Balner123/GPS_server_NodeJS/docs&LaTex/docs_server/0-packages.md

Below is a human-friendly summary of the main dependencies used by the project. For exact versions see `package.json`.

Dependencies:

- `bcryptjs` — password hashing
- `connect-flash` — flash messages for web UI
- `cors` — Cross-Origin Resource Sharing helper
- `dotenv` — load env vars from `.env`
- `ejs` — server-side view templates
- `express` — web framework
- `express-rate-limit` — rate limiting middleware
- `express-session` — session management
- `express-validator` — request validation
- `mysql2` — MySQL driver for Sequelize
- `nodemailer` — sending emails (verification, notifications)
- `passport` — authentication framework
- `passport-github2` — GitHub OAuth strategy
- `passport-google-oauth20` — Google OAuth strategy
- `sequelize` — ORM for MySQL
- `swagger-jsdoc` — JSDoc -> OpenAPI generation
- `swagger-ui-express` — serve Swagger UI

DevDependencies:

- `nodemon` — automatic server restart during development

Installation (from `package.json`):

- `npm install`
