Balner123/GPS_server_NodeJS/LilyGO-T-A76XX-main/MAIN/FINAL/docs_hw/4-data-format.md

# Formát dat a API

Tento dokument definuje přesnou podobu datových payloadů a chování komunikace mezi firmwarem a backendem. Preferujte krátké a stálé JSON payloady; rozsáhlejší ukázky uložte jako vzory v `docs_hw/schemas/`.

## Endpointy

- Upload dat: `POST http(s)://<server>[:<port>]/api/devices/input`
- Handshake: `POST http(s)://<server>[:<port>]/api/devices/handshake`
- Registrace (OTA): `POST http(s)://<server>[:<port>]/api/devices/register`

Poznámka: port 80 značí HTTP, jiný port než 443 znamená explicitně uvedené portování v URL; preferujte HTTPS.

## Struktura uploadu

Upload probíhá dávkově — jako pole JSON objektů. Každý objekt reprezentuje buď polohový záznam, nebo stavový záznam (např. potvrzení `power_status`).

Schematický příklad záznamu polohy (stručný):

```json
{
	"device": "<installationId>",
	"name": "<deviceName>",
	"latitude": <number>,
	"longitude": <number>,
	"speed": <number>,
	"altitude": <number>,
	"accuracy": <number>,
	"satellites": <number>,
	"power_status": "ON|OFF",
	"timestamp": "2025-01-01T12:00:00Z"
}
```

Stavový záznam (příklad):

```json
{
	"device": "<installationId>",
	"power_status": "OFF"
}
```

Poznámky k polím:
- `device` — identifikátor zařízení (posledních 10 hex znaků MAC bez dvojteček).
- `timestamp` — musí být ISO 8601 v UTC; interně se drží epoch milliseconds a serializuje se při odeslání.

## Dávkování a trvaní session

- `send_cached_data()` čte maximálně 15 záznamů na jeden upload (implementační limit `MAX_BATCH_SIZE`). Poznámka: server je navržen tak, aby bezpečně zpracoval až 15 položek; větší dávky mohou způsobit HTTP 500.
- Po úspěšném potvrzení jsou odeslané položky z cache odstraněny; neúspěšné položky zůstávají pro opakování.
- V průběhu jedné GPRS session probíhá nejprve handshake a následně upload dat.

## Formát odpovědi

Typická odpověď backendu (stručná):

```json
{
	"success": true,
	"registered": true,
	"config": {
		"interval_gps": 120,
		"interval_send": 5,
		"satellites": 4,
		"mode": "batch"
	}
}
```

- `success` — indikace přijetí dávky.
- `registered` — pokud `false`, zařízení přechází do bezpečného režimu.
- `config` — volitelné parametry, které zařízení aplikuje okamžitě.

HTTP stavové kódy a chování:
- 200: standardní odpověď s JSON → aplikovat konfiguraci.
- 403: vyžadovat odhlášení (FORCE_LOGOUT).
- 404/409: považovat za neregistrované zařízení → přepnout `registered=false`.
- ≥500 nebo síťová chyba: zachovat data v cache a opakovat později.

## Handshake

Handshake se provádí vždy před odesíláním dat v rámci GPRS session. Odesílaný payload (stručně):

```json
{
	"device_id": "<installationId>",
	"client_type": "HW",
	"power_status": "ON|OFF"
}
```

Odpověď může obsahovat pole `registered`, `config` a `power_instruction` (`TURN_OFF` / `NONE`). Hodnota `TURN_OFF` by měla vést k potvrzení a následnému řízenému vypnutí.

## Registrace (OTA)

Endpoint `/api/devices/register` přijímá registrační payload obsahující `client_type`, `username`, `password`, `device_id` a `name`. Registrace vyžaduje aktivní GPRS spojení; po úspěchu se doporučuje restart do běžného režimu.

## Chování při chybách

- Neparsovatelná odpověď: logovat chybu, zachovat data v cache.
- Kritické chyby (`404`, `409`): přepnout `registered=false` a čekat na servisní zásah.
- Síťové chyby a 5xx: zachovat data a opakovat během dalšího cyklu.
