Balner123/GPS_server_NodeJS/docs&LaTex/requirements_examples/lacheta_zaverecna-prace.md

Zde je kompletnì zpracovaný dokument do formátu **Markdown**. Zachoval jsem strukturu nadpisù, zvýraznìní kódu (C++) a formátování seznamù.

***

# ZÁVÌREÈNÁ STUDIJNÍ PRÁCE
## Dokumentace: Robotická ruka s využitím EMG

**Škola:** SŠPU Opava (Støední škola prùmyslová a umìlecká, Opava)  
**Autor:** Václav Lacheta  
**Obor:** 18-20-M/01 INFORMAÈNÍ TECHNOLOGIE se zamìøením na poèítaèové sítì a programování  
**Tøída:** IT4  
**Školní rok:** 2021/2022

---

### Podìkování
Dìkuji doc. Ing. Petru Èermákovi, Ph.D. za odborné konzultace a rady, které mi poskytl bìhem øešení mého projektu.

### Prohlášení
Prohlašuji, že jsem závìreènou práci vypracoval samostatnì a uvedl veškeré použité informaèní zdroje.

Souhlasím, aby tato studijní práce byla použita k výukovým úèelùm na Støední prùmyslové a umìlecké škole v Opavì, Praskova 399/8.

**V Opavì 31. 12. 2021**  
*(podpis autora práce)*

---

## ANOTACE

Souèástí práce bylo sestavení protetické ruky InMoov v životní velikosti ze souèástek vytisknutých na 3D tiskárnì. Umìlá ruka je ovládána pomocí elektromyografických (EMG) senzorù, díky nimž je možné získávat elektrické svalové signály a pøevádìt je na mechanické pohyby napodobující chování skuteèné lidské ruky. Ruka je upevnìna na podstavci obsahujícím nezbytný hardware vèetnì displeje a rotaèního enkodéru, který lze použít k ovládání. Zaøízení je možné ovládat manuálnì (natoèit každý prst do libovolného úhlu), pomocí EMG senzorù nebo zvolit nìkteré z naprogramovaných gest.

**Klíèová slova:** EMG, elektromyografie, InMoov, myoelektrická protéza, rotaèní enkodér, servomotor, Arduino, 3D tisk, displej

---

## OBSAH

1. **PROTÉZY**
    *   1.1 Historie protéz
    *   1.2 Klasifikace protéz
    *   1.3 Pasivní protézy
    *   1.4 Aktivní protézy
        *   1.4.1 Protézy pohánìné tìlem
        *   1.4.2 Myoelektrické protézy
        *   1.4.3 Hybridní protézy
2. **ELEKTROMYOGRAFIE**
    *   2.1 Svaly horní konèetiny
    *   2.2 EMG signály
    *   2.3 Snímání EMG signálù
3. **MOŽNÉ ZPÙSOBY ZPRACOVÁNÍ EMG SIGNÁLU A JEJICH IMPLEMENTACE V PROTÉZÁCH**
    *   3.1 Mikrokontrolery
    *   3.2 Senzory
    *   3.3 Pøíklady protéz
        *   3.3.1 Inteligentní humanoidní robotická ruka Sain
        *   3.3.2 Protetická ruka InMoov
4. **SESTROJENÍ RUKY**
    *   4.1 InMoov ruka
    *   4.2 Ovládaní servo motorù
    *   4.3 Ovládaní ruky pomocí EMG
    *   4.4 Displej a uživatelské ovládaní
    *   4.5 Podstavec
    *   4.6 Využité souèástky
*   **ZÁVÌR**
*   **SEZNAM POUŽITÝCH INFORMAÈNÍCH ZDROJÙ**
*   **SEZNAM PØÍLOH**

---

## ÚVOD

Nad výbìrem závìreèné práce jsem pøemýšlel dlouhou dobu. Hledal jsem takový projekt, pøi jehož øešení bych mohl uplatnit své znalosti programování mikrokontrolerù a využít i rozmanitou zásobu elektronických souèástek, které jsem nashromáždil v prùbìhu svého studia na støední škole. Zároveò jsem si pøál pustit se také do nìèeho nového, co by pøedstavovalo zajímavou výzvu pro mì samotného a pøípadnì bylo pøínosné i pro druhé.

Jednoho dne jsem zhlédl video s ukázkou robotické ruky, která se ovládá pomocí EMG senzorù. V tu chvíli jsem se rozhodl, že právì to bude téma mého závìreèného projektu. Navíc jsem vždy tento typ protézy považoval za nìco, co si nemùže normální smrtelník sestavit doma, takže jsem byl i hodnì zvìdavý, zda se mi to povede.

Nyní tedy pøedkládám výsledek své práce, která trvala nìkolik mìsícù. Podaøilo se mi dosáhnout vìtšiny dílèích cílù, které jsem si vytyèil. Z finanèních dùvodù jsem si bohužel nemohl dovolit poøídit více EMG senzorù a musel jsem si vystaèit pouze s jedním, pomocí kterého dokáži monitorovat sevøení nebo otevøení pìsti a následnì tento pohyb pøevést na robotickou ruku.

V praxi se s mým øešením moc nesetkáme, tento zpùsob se spíše využívá ve svìtì medicíny a bioinformatiky pro diagnostiku. Vyspìlejší protézy se spíše zamìøují na umístìní elektrod uvnitø svalu, jelikož jsou získávány mnohem pøesnìjší signály.

V úvodní kapitole své dokumentace se zabývám vývojem protéz v historii a popisuji nìkterá zajímavá technická øešení, která se objevila v minulosti i ta, která se používají dnes. Další èást je zamìøena na problematiku elektromyografie, jež studuje strukturu kosterní svaloviny a elektrické biosignály, které ze svalù vycházejí. Díky poznatkùm tohoto oboru mùžeme využívat EMG senzory a snímat pomocí nich impulzy lidského tìla. Nejdùležitìjší èást mé práce je podrobnìji vìnována technickému a programovému øešení projektu InMoov ruky.

---

# 1. PROTÉZY

Protézu lze definovat jako „umìlé zaøízení, které nahrazuje nebo doplòuje chybìjící èi narušenou èást lidského tìla“.

V dnešní dobì existuje mnoho rùzných typù protéz. Ty se pohybují od kosmetických ozdob pøes jednoduché pasivní mechanické pomùcky, jako jsou rùzné háky a podobnì, až po elektricky pohánìné protézy, které mohou alespoò èásteènì obnovit funkci chybìjící konèetiny.

## 1.1 Historie protéz
Myšlenka umìlého nahrazení ztracených konèetin existuje již tisíce let. Existují protézy, které jsou více než 3000 let staré. Pøíkladem je takzvaný „káhirský prst“, který byl nalezen u egyptské mumie a mìl nahradit ztracený palec u nohy. Protézy, jako je tato, byly kdysi vyrábìny pomocí pøírodních surovin: kùže, døeva èi lnu.

*Obrázek 1: Káhirský prst*

V roce 300 pøed naším letopoètem byla Øímany vyrobena první známá protetická noha, takzvaná „noha Capua“. Byla vyrobena ze železa a bronzu a mìla døevìné jádro. Bìhem této doby se objevily protézy, jako jsou ruèní háky a kolíkové nohy, které umožòovaly chùzi nebo držení štítù. Ty byly sestrojeny pøevážnì ze železa a oceli.

V dobì renesance udìlala anestezie a léèba ran veliký pokrok, amputace proto byly bezpeènìjší než kdy døíve. S novými možnostmi amputace se zaèaly šíøit vynálezy, jakým byl napøíklad tzv. turniket, které pomohly zastavit tìžké krvácení v prùbìhu amputace. Vznikaly nové typy protéz - napøíklad „železná ruka rytíøe Götz von Berlichingen“, s níž bylo možné pohybovat a manipulovat pomocí pružinového mechanismu uvnitø ruky. V této dobì se na protézy používalo pøedevším železo, ocel, mìï a døevo.

V období americké obèanské války, ale i bìhem svìtových válek zažila protetika velký posun vpøed vyplývající z vysokého poètu zmrzaèených vojákù. Kromì toho byl vyvinut i zcela nový materiál - pryž, který doplòoval døívìjší protézy ze døeva a kùže.

V letech po druhé svìtové válce bylo objeveno mnoho dalších materiálù, díky kterým se døevo a kùže staly nepotøebnými. Patøí mezi nì pryskyøice, polykarbonát, plast a lamináty. Díky jejich použití se protézy staly lehèí a odolnìjší.

Materiálové složení se v posledních letech dále zdokonaluje a v souèasnosti vznikají vysoce výkonné protézy, které mají vyšší stabilitu, pohodlí a nižší hmotnost. Kromì toho mohou být souèástí protéz senzory umožòující aktivní ovládaní pomocí mikroprocesorù. Vývoj moderních protéz se mùže opøít i o nové výrobní procesy, jako je 3D tisk, který umožòuje vyrobit velmi jednoduché i levné protézy.

*Obrázek 1.2: Noha Capua | Obrázek 1.3: Ruka Götz von Berlichingen*

## 1.2 Klasifikace protéz
Protézy mùžeme rozdìlit na:

1.  **Pasivní.** Protézy, které nemají žádné pohyblivé èásti. Ty se vìtšinou používají pro estetické úèely. Existují také protézy urèené pro speciální úkoly, jako je zahradnièení nebo sport.
2.  **Aktivní.** Ty jsou naopak urèeny k podpoøe vyšší produktivity a funkènosti. Mají pohyblivé èásti, které jsou pohánìny buï samotným tìlem, nebo vnìjší energií. Navíc existují ještì hybridní kombinace, které jsou pohánìny èásteènì tìlem a èásteènì akèními èleny.

*Obrázek 1.4: Rozdìlení protéz*

Protézy mohou plnit dva rùzné úkoly, které se mohou zásadnì lišit. Na jednu stranu, protézy mají obnovit funkce, které byly ztraceny ztrátou konèetiny a na druhou stranu se protézy používají k optické obnovì „normálního stavu“ tìla. Protézy, které vizuálnì pøipomínají chybìjící konèetinu, mají èasto omezenou funkènost, zatímco funkèní protézy nejsou moc dobré po vizuální stránce. Proto existuje mnoho pacientù, kteøí mají nìkolik rùzných protéz, napøíklad jednu, která vizuálnì pøipomíná chybìjící konèetinu, a druhou, která je maximálnì funkèní.

## 1.3 Pasivní protézy
Kosmetické použití protéz je velmi dùležité, protože zejména horní konèetiny jsou èasto používané v sociálních interakcích, jako jsou gesta nebo bìhem komunikace. Vizuálnì nenápadný vzhled tak mùže pomoci vyhnout se psychickému stresu z dùvodu odlišnosti od ostatních. To platí zejména v pøípadì, kdy amputací není postiženo pouze pøedloktí, ale i paže. Nejlepší reprezentace pøirozené ruky poskytují pasivní kosmetické protézy. Lze je pøizpùsobit pacientovi pomocí tvaru a barvy; napøíklad napodobit barvu kùže a anatomické rysy, jako jsou znaménka, nebo dokonce ochlupení na pažích. Estetické protézy lze také použít pro jednoduché manuální úkoly, jako je fixace papíru pøi psaní. Obecnì jsou velmi lehké a mají vysoký komfort nošení.

*Obrázek 1.5: Pøíklad pasivní protézy*

## 1.4 Aktivní protézy
Nejèastìji se vyskytují protézy aktivní. Tyto mají pohyblivé èástí, které jsou pohánìny buï tìlem, nebo vlastním zdrojem energie. S tìlesnì pohánìnými protézami se ovládání provádí pohybem svalu v blízkosti amputované konèetiny. U myoelektrických protéz jsou akèní potenciály svalu monitorovány senzory a použity pro pohyb protézy. Aktivní protézy mohou mít mnoho podob, jako napøíklad ruce, pohyblivé háky nebo speciální tvary pro konkrétní pacienty. Tento druh protéz je obvykle tìžší než pasivní, jelikož jsou pro nì urèeny vìtší zátìže. Díky tomu jsou èasto vyrobeny z tìžších, ale odolnìjších materiálù, jako jsou kov nebo tvrzený plast. Úkolem aktivních protéz je obnovit funkènost postižených konèetin, a zejména ruka má velký význam pro manipulaci s objekty. Pomocí takových protéz je možné uchopovat pøedmìty a zvládat èinnosti v každodenním životì.

### 1.4.1 Protézy pohánìné tìlem
Protézy pohánìné tìlem jsou èasto oznaèovány jako „ovládané kabelem“, protože vyžadují ocelové kabely bìhem provozu. Obvykle jsou tyto postroje konstruovány tak, že popruh prochází pøes lopatku a pøipojuje se k tažnému lanku, které ovládá protézu. Protože protézy pohánìné tìlem jsou pøímo spojeny napøíklad s pohybem ramena, mají tak vysokou úroveò zpìtné vazby na základì napìtí na ovládacím kabelu. Dalšími výhodami tìchto protéz je, že jsou ve vìtšinì pøípadù vodotìsné a snadno se èistí. Jejich jednoduchý design umožnuje postiženým osobám se je rychleji nauèit ovládat, a navíc stojí výraznì ménì ve srovnání s aktivnì øízenými.

Nevýhodou tìchto protéz je, že k ovládání potøebují postroj k ovládání. To znamená, že postižené osoby musí mít urèitou sílu a svobodu pohybu, aby mohly takové zaøízení ovládat. Navíc jsou tyto protézy èasto vizuálnì ménì pøitažlivé ve srovnání s elektricky pohánìné, a to kvùli postroji.

Protézy s takovým mechanickým pøenosem síly jsou oblíbenìjší než ty elektrické. Devadesát procent lidí, kteøí mají aktivní protézu, používají protézu pohánìnou tìlem. Jejich nejvìtšími klady jsou nízká hmotnost, odolná konstrukce a lepší haptická odezva generovaná kabely.

*Obrázek 1.6: Pøíklad protézy pohánìné tìlem*

### 1.4.2 Myoelektrické protézy
Tyto protézy jsou pøevážnì elektrické. Mají externí zásobník energie, který napájí vestavìné akèní èleny. Obecnì se energie ukládá ve formì akumulátoru. Tato zaøízení lze ovládat více vstupy, jako jsou elektromyografické (EMG) signály, zpìtná vazba motorù a také vyhrazené spínaèe. Takové fyzické spínaèe jsou zvláštì užiteèné u vážných amputací. Je to proto, že v takových pøípadech obvykle existuje mnoho rùzných motorù, jsou zapotøebí rùzné spoje a je tøeba je ovládat samostatnì.

Nicménì myoelektrické protézy se ještì èastìji používají u ménì vážných amputací. Myoelektrické protézy jsou založeny na mìøení elektrického vzruchu ve svalech. Elektrody pøipojené ke svalùm mìøí elektrické signály z kontrakcí kosterního svalstva. Zmìny elektromagnetických polí, které vznikají pøi napnutí svalu, zachycuje povrch elektrody a jsou v podobì napì�ových signálù posílány do mikrokontroleru.

Ve vìtšinì pøípadù jsou elektrody pøipevnìny ke dvìma svalùm, které vykonávají pohyb v urèitém smìru, jako je extenzor zápìstí a flexor zápìstí. Pro tento úèel se používá jeden sval pro jeden smìr pohybu protézy. Napøíklad napnutím jednoho svalu se otevøe dlaò a napnutí protikusu se dlaò uzavøe. Aby se zabránilo nedobrovolným pohybùm, jsou pro signály EMG nastaveny prahové hodnoty. Teprve po pøekroèení urèitého prahu se protéza zaène pohybovat.

Jednou z výhod takové myoelektrické protézy je, že umožòuje vìtší uchopovací síly ve srovnání s protézami pohánìnými tìlem. V nìkterých pøípadech to mùže být výhodné pøi držení objektù na delší dobu. Kromì toho nejsou pro úèely ovládání potøeba žádné postroje. To dovoluje ovládání více os a kloubù souèasnì. Absence postroje také umožòuje, aby vypadaly více jako skuteèné konèetiny.

Existují však také dùvody, proè jsou protézy pohánìné tìlem 10krát populárnìjší než myoelektrické. Je to dáno pøedevším vyšší poøizovací cenou takových zaøízení. Navíc jsou ménì robustní a kvùli vestavìné elektronice jen èásteènì vodotìsné. Protože mezi nimi není žádné mechanické spojení zbývající konèetiny s protézou, je haptická zpìtná vazba horší. Nìkdy je pro postižené tìžší, aby správnì vyhodnotili a použili požadovanou uchopovací sílu. Kromì toho se tyto protézy kvùli složité konstrukci snadnìji lámou a musí být èastìji servisovány.

Elektrody jsou jejich další nevýhodou, nebo� se mùže stát, že se pohnou nebo ztratí kontakt. V tìchto pøípadech nelze protézy správnì provozovat. Konstantní kontakt s elektrodami mùže také zpùsobit podráždìní kùže nebo nepøíjemný pocit, pokud protéza není správnì upravená. Pøesto se tyto protézy neustále vyvíjejí a mohly by být v budoucnu více rozšíøené.

*Obrázek 1.7: Myoelektrická protéza*

### 1.4.3 Hybridní protézy
Existují i protézy, které se skládají z kombinace tìlesnì pohánìných a myoelektrických. Tato kombinace umožòuje využít výhody obou typù, napøíklad mohou dosáhnout vysokých uchopovacích sil pøi zachování nízké hmotnosti protézy. Navíc tento pøístup mùže usnadnit ovládání protézy.

---

# 2. ELEKTROMYOGRAFIE

## 2.1 Svaly horní konèetiny
Kosterní svaly jsou souèástí svalstva odpovìdné za aktivní pohyby tìla, a tedy i souèástí jednoho ze tøí hlavních typù svalù. Stejnì jako srdeèní svaly patøí kosterní svaly do skupiny pøíènì pruhovaných svalù a oznaèují se také jako dobrovolné svaly. Až na pár výjimek, jsou tyto svaly napojeny na kost šlachami. Èasto existují v párech, pøièemž první sval je primárním hybatelem a druhý je jeho antagonistou. Napøíklad, biceps a triceps jsou taková dvojice antagonistù. Když se jeden z nich stáhne, druhý se uvolní a umožní pohyb a naopak.

Kosterní svaly mají složitou strukturu. Skládají se z fasciklù, které jsou svazky prodloužených svalových vláken. Samotná svalová vlákna se skládají ze svazkù myofibril. Samotné myofibrily jsou tvoøeny z myozinových a aktinových vláken. Tato dvì vlákna jsou naskládaná v pravidelnì se opakujících sestavách a jsou zodpovìdná za samotnou kontrakci svalù klouzáním proti sobì navzájem. Tato myozinová pole se nazývají sarkomery. Motorické neurony, které øídí kontrakci, jsou spojeny ve snopci svalových vláken a spoleènì se nazývají motorická jednotka.

**Nejdùležitìjší svaly jsou:**
1.  *Musculus pectoralis major* (velký sval prsní)
2.  *Musculus deltoideus* (deltový sval)
3.  *Musculus bizeps brachii* (dvojhlavý sval pažní)
4.  *Musculus trizeps brachii* (trojhlavý sval pažní)
5.  *Musculus brachioradialis* (sval vøetenní)
6.  *Musculus flexor digiti* (sval který zajištuje ohýbaní prstù)

*Obrázek 2.1: Svaly horní konèetiny*

Motorické neurony se nacházejí uvnitø mozkového kmene a míchy a jsou spojeny se svalem pøes axony, který mohou pøenášet excitaèní signál na velké vzdálenosti. Aktivace svalových vláken se dìje elektrickými potenciály bunìèných membrán. Díky otevíráním a zavíráním iontových kanálù umožòují membrány pohyb iontù a vytvoøit tak signál elektromagnetického pole. Tento signál cestuje podél axonù jako vlna a skonèí v motorickém neuronu. Místo, kde se motorické neurony spojují se svalovými vlákny, se nazývá neuromuskulární spojení. To je místo, kde vlákna zaènou reagovat na signál motorického neuronu a tím zaènou kontrakce.

*Obrázek 2.2: Struktura kosterního svalu*

## 2.2 EMG signály
Akèní potenciály se vytváøejí bìhem kontrakce kosterní svaloviny. Tyto akèní potenciály se dají mìøit a jsou také základem EMG signálù. EMG signály jsou používané pro analýzu a klinickou diagnostiku v biomedicínských aplikacích, jako jsou rehabilitace pohybových vad. Elektrické proudy generované bìhem procesu flexe lze mìøit pomocí elektrod na svalu nebo uvnitø svalu. EMG signály jsou pomìrnì komplikované, protože jsou závislé na anatomii fyziologické vlastnosti svalu. Neèistoty tìchto signálù jsou zcela bìžné a hromadí se pøi cestování tìlem. Signál EMG je také sumou nìkolika motorických jednotek, které vysílají ve stejnou dobu, a tak mùže docházet k interakcím mezi tìmito rùznými signály.

Intervaly, ve kterých se vyskytují akèní potenciály konkrétní motorické jednotky, jsou náhodné. Samotný akèní potenciál motorické jednotky je kombinací akèních potenciálù svalových vláken patøící k jedné motorické jednotce. Lze to popsat vzorcem níže:

$$x(n) = \sum_{r=0}^{N-1} h(r)e(n-r) + w(n)$$

V tomto vzorci je:
*   `x(n)` výsledný EMG signál,
*   `e(n)` impuls odpalu n,
*   `h(r)` akèní potenciál motorické jednotky,
*   `w(n)` aditivní bílý Gaussùv šum,
*   `N` poèet støel motorických jednotek.

*Obrázek 2.3: Dekompozice EMG signálu*

## 2.3 Snímání EMG signálù
EMG signály jsou snímány elektrodami, které jsou buï umístìny na kùži nad svalem, nebo uvnitø svalu. Obì varianty mají svá pro a proti. Pøi použití intramuskulárních senzorù musí být prostøedí a senzory sterilizovány, protože se jedná o invazivní postup, který nese velké riziko pøenosu nemoci nebo spuštìní infekce. Na druhou stranu, jakmile je elektroda umístìna, tak nezpùsobuje žádné nepohodlí a signály nejsou zkresleny tkánìmi svalù a kùže. Tento proces vede k vìtší èistosti signálu nad šumem.

Na druhou stranu, povrchové elektrody mohou být kdykoliv pøemístìny, pokud poloha není vhodná a nepotøebuje k tomu žádné invazivní postupy. Vìtšinou se povrchové elektrody využívají pro krátká mìøení. Je velmi dùležité elektrody správnì umístit a používat elektrody pro konkrétní úkol, výbìr místa totiž velice ovlivní získaný signál. Chceme-li získat nejvyšší sílu signálu, tak elektrody musí být umístìny uprostøed svalu ve smìru svalových vláken. Nejèastìjší používané elektrody jsou Ag/AgCL, protože nejsou polarizovatelné a umožnují proudový tok kùže. Ve vìtšinì pøípadù jsou pøipevnìny pomocí vodivého gelu pro snížení impedanci kùže.

Obvykle se používají `2n + 1` elektrody. Dvì pro každý kanál `n` a jedna referenèní (uzemòovací) elektroda, která je umístìna na elektricky nesouvisející tkání.

Poté, co je signál zachycen, je obvykle zesílen, protože jeho amplituda je pomìrnì malá. Pro první etapu zesílení se bìžnì používá diferenciální zesilovaè. Diferenciální zesilovaè se používá k eliminaci spoleèných proudù. Signál je snímán na tøech místech, dvì detekèní elektrody a jedna referenèní, která definuje neutrální zem, kterou sdílejí další dvì elektrody. Jakýkoliv spoleèný signál pro tyto dvì elektrody bude odstranìn, naopak signály, které nesdílejí, budou poté zesíleny.

Poté se použije zesilovaè k dalšímu zvýšení amplitudy signálu. Pro eliminaci vysokého šumu se používá pláš� nízko propustného filtru frekvence. Dále lze použít usmìrnìní signálu pro pøeklopení èástí negativního signálu na pozitivní. Nakonec je použit A/D pøevodník, aby poèítaè nebo mikrokontroler mohl pracovat se signálem EMG.

*Obrázek 2.4: Schéma nahrávaní EMG*

---

# 3. MOŽNÉ ZPÙSOBY ZPRACOVÁNÍ EMG SIGNÁLU A JEJICH IMPLEMENTACE V PROTÉZÁCH

## 3.1 Mikrokontrolery
Je na výbìr nìkolik možností. První možností je použít mikrokontroler k mìøení svalové aktivity a vyhodnocování signálu. Napøíklad Arduino Uno je založeno na èipu ATMEL ATmega328, pracuje na frekvenci 16 MHz a mùže komunikovat s ostatními zaøízeními pøes UART, SPI a I2C. Kromì toho vstupní a výstupní (GPIO) piny lze použít k ovládání rùzných dalších periferií nebo ke ètení analogových a digitálních signálù díky vestavìnému 10bitovému A/D pøevodníku. Další výhodou tìchto vývojových desek je, že je lze jednoduše programovat a nevyžadují vyhrazené pøístupy a bitové manipulace jednotlivých registrù, navíc jsou takové desky dost rozšíøené, snadno dostupné a existuje velké množství už vytvoøených kódù a dokumentací pro další usnadnìní programování.

Nevýhodou však bývá výkon použitých procesorù, protože musí být co nejmenší a energeticky efektivní, mají èasto jen omezený výkon. To znamená, že na tìchto zaøízeních lze provádìt pouze jednoduché matematické operace, a to mùže mít významný dopad na výkon celého systému, zejména pro aplikace v reálném èase, jako je EMG analýza. Kvùli nízkému výkonu nemusí být signály naèteny vèas a zpracování mùže trvat déle, což má za následek velké zpoždìní v celém systému nebo omezenou funkènost, proto je lepší se dívat po dalších výkonnìjších mikrokontrolerech.

## 3.2 Senzory
Prvním krokem pøi získávání dat je identifikace správných pozic pro elektrody. Aby bylo možné správnì rozeznávat pohyby jednotlivých prstù, je potøeba použít nìkolik svalových signálù. Na monitorování každého prstu je potøeba minimálnì 4 senzory èili 4 kanály. Jeden pro palec, jeden pro prostøedníèek, jeden pro ukazováèek a jeden senzor pro prsteníèek a malíèek dohromady. Nejlépe je použít 5 senzorù, aby mìl každý prst vyhrazený kanál.

Celkem máme tedy 11 elektrod. Pìt párù po dvou elektrodách a další referenèní elektrodu. Tato referenèní elektroda je umístìna na zadní stranì pøedloktí v úrovni loktu, protože tam se dá oèekávat malá svalová aktivita, nebo na kosterní èásti ruky. Senzory jsou poté pøipojeny k samotným elektrodám, aby zesílily a pøenesly signál do mikrokontroleru.

V dnešní dobì jsou EMG senzory pomìrnì dost rozšíøené a máme na výbìr hned nìkolik rùzných senzorù od rùzných firem. Ve své práci jsem použil senzory **MyoWare od Advancer Technologies**. Tyto senzory lze provozovat pro napìtí 3,3 V nebo 5 V. Logika zpracování svalového signálu je øešena pøímo na senzorech, tudíž z nich mùžeme èíst obálku signálu. Pokud je pro tuto funkci nechceme použit, mùžeme zachytit i surový EMG signál a zpracování si øešit potom sami. Zesílení signálu lze nastavit pomocí potenciometru. Výstupní analogový signál už potom èteme a zpracováváme na mikrokontroleru.

*Obrázek 3.1: Myoware muscle sensor*

## 3.3 Pøíklady protéz

### 3.3.1 Inteligentní humanoidní robotická ruka Sain
Tato robotická ruka se dá velmi snadno používat, protože už je pøedem složená.

*Obrázek 3.2: Sain Smart 5-DOF*

### 3.3.2 Protetická ruka InMoov
Protetická ruka InMoov nabízí lepší zpùsob zobrazení pohybù. Je souèástí projektu s otevøeným zdrojovým kódem, který založil francouzský sochaø a designér Gael Langevin. Projekt InMoov se skládá ze stovek 3D tisknutých dílù, které lze pøipojit k pohonùm a vytvoøit tak robota v životní velikosti. Jednotlivé konèetiny lze ovládat a rozpohybovat pomocí motorù. Stejnì jako u ruky Sain Smart lze prsty ovládat jednotlivì. To se také provádí pomocí 5 serv, které se montují do pøedloktí a ovládají prst pøes provázky. Jedno servo mùže být použito k otáèení ruky kolem zápìstí. Ve srovnání s rukou Sain Smart používají InMoov vìtší a mnohem silnìjší serva. Kromì toho návrh prošel nìkolika designovými iteracemi a neustále se pøizpùsobuje a zlepšuje.

*Obrázek 3.3: Robot InMoov*

---

# 4. SESTROJENÍ RUKY

Kompletní sestrojení ruky se rozdìlovalo na více èástí.
*   Sestrojení mechanické èasti ruky.
*   Ovládaní servo pohonù na ruce.
*   Ovládání pomocí EMG senzorù.
*   Ovládaní pøes uživatelské rozhraní.
*   Sestrojení podstavce pro zlepšení vzhledu a manipulace.

## 4.1 InMoov ruka
Pro svùj projekt jsem zvolil sestrojení protetické ruky InMoov. Na InMoov webu jsou dostupné všechny díly a také podrobný návod jak ruku složit. Celá ruka se skládá z 50 rùzných dílù. Díly jsou vytisknuté z PETG materiálu. Vìtšinou se díly lepily k sobì, ale nìkteré jsou i našroubované.

Ve spodní èásti ruky je pøimontovaných pìt MG995 servo pohonù, které pohybují s prsty. Další MG995 servo je pøimontované v zápìstí pro otáèení dlanì.

Èlánky prstù jsou k sobì lepené a pro klouby je využita válcovitá tyè o prùmìru 3 mm, která slouží jako èep. Èlánky prstu jsou pøes pomocné vodicí díry propleteny vždy dva stejnì dlouhé rybáøské pletence. Na koneècích prstù jsou dva provázky svázané k sobì, aby utvoøily jeden.

Dále jsou provázky propletené pøes dlaò až po zápìstí a tam jsou navázané na serva, které je napínají a tím napodobují funkci šlachy: když servo zatáhne za jeden konec provázku, prst se ohne a když zatáhne za druhý, tak se prst znova otevøe.

*Obrázek 4.1: Díly k ruce | Obrázek 4.2: Spodní èást ruky | Obrázek 4.3: Servo na otáèení dlanì | Obrázek 4.4: Dlaò | Obrázek 4.5: Koneèky prstù | Obrázek 4.6: Propletení provázku pøes ruku*

Provázky jsou namotané na kroužky servo motorù a pomoci dvou šroubkù se provázek napne. Všechna serva ovládá Micro Maestro 6-Channel od Pololu, který komunikuje s Arduinem pøes protokol UART.

*Obrázek 4.7: Sestavená ruka*

## 4.2 Ovládaní servo motorù
Micro Maestro, které ovládá servo pohony a Arduino spolu komunikují pomocí protokolu UART èili pøes RX a TX piny na desce. Protože Arduino UNO má dva vyhrazené RX a TX piny, které jsou potøeba pro nahrávání kódu, tak si je simuluji na jiných pinech pomocí knihovny `SoftwareSerial.h`.

Díky knihovnì pro Micro Maestro už šlo samotné programování pohybu serv jednoduše. Pro zefektivnìní a pro lepší pøehlednost kódu jsem vytvoøil tøidu `Arm`, která obsahuje veškeré potøebné metody k ovládaní serv, jako jsou `openIndex()`, `closeIndex()`, `getIndexPos()` a další.

```cpp
void Arm::openPinky()const{
    maestro.setTarget(this->pinky,this->open);
    return;
}

void Arm::closeThumb()const{
    maestro.setTarget(this->thumb, close);
    return;
}
```

## 4.3 Ovládaní ruky pomocí EMG
Mým cílem bylo monitorovat každý prst, ale v prùbìhu jsem zjistil, že tento cíl je dosti vzdálený z dùvodu nedostatku financí. Cena tìchto senzorù je pomìrnì dost vysoká.

Rozhodl jsem se proto pro jednodušší øešení pouze s jedním senzorem a monitorování otevøení a sevøení pìsti. Èást kódu, která se stará o ovládání ruky pomoci EMG senzorù, je pomìrnì dost jednoduchá. Když si necháme vypisovat hodnoty ze senzorù na graf, tak dostaneme takovýto výsledek.

Z grafu jde vidìt, že když zatneme pìst, tak hodnota rapidnì vzroste, protože v tu chvíli projde pøes senzor elektrický proud. Poté jsou hodnoty zase nízké, i když držíme zatnutou pìst. Hodnota opìt vzroste, když pìst uvolníme.

Èili když hodnota bude vìtší než naše nastavená prahová hodnota, tak se pohne servy tak, aby utvoøily pìst.

*Obrázek 4.8: Graf EMG hodnot | Obrázek 4.9: Graf EMG hodnot (detail)*

Problémem je, že nevíme, kdy má uživatel sevøenou pìst a kdy ne, protože nárùsty hodnot jsou témìø stejné v obou pøípadech. Èili pro moje øešení jsem použil jednoduchý pøepínaè, který pøepíná mezi stavy pìst a dlaò. Nárùst hodnoty trvá nìjakou chvílí, takže ještì pøed pøepnutím stavu se poèká 250 ms, než k nìmu dojde.

```cpp
void sensor() {
    // Read the values from EMG sensor
    sensorValue = analogRead(A0);
    unsigned long currentMillis = millis();

    // Swap for fist flag
    if (sensorValue >= sensorTreshold && sensorFist == 0) {
        // Wait some time to prevent unwanted switching
        if (currentMillis - prevMillis > sensInterval) {
            sensorFist = 1;
            prevMillis = currentMillis;
        }
    } else if (sensorValue >= sensorTreshold && sensorFist == 1) {
        if (currentMillis - prevMillis > sensInterval) {
            sensorFist = 0;
            prevMillis = currentMillis;
        }
    }
}
```

## 4.4 Displej a uživatelské ovládaní
Ruka má k dispozici i uživatelské ovládání, kdy si na displeji mùže pomocí rotaèního enkodéru uživatel vybrat mezi rùznými módy ovládání:

1.  **Manuální** – v tomto modu si mùže uživatel natoèit jednotlivý prst do urèitého úhlu ruènì.
2.  **EMG** – zde se bude ruka ovládat pomocí EMG senzorù. Uživatel zde mùže vidìt i aktuální hodnotu senzoru a také si upravit hranièní hodnotu, pøi které má ruka sevøít pìst.
3.  **Gesta** – zde si mùže uživatel vybrat mezi rùznými pøed-programovanými gesty.

*Obrázek 4.11: Ukázka uživatelského ovládaní*

## 4.5 Podstavec
Myšlenka podstavce se zrodila hlavnì proto, aby došlo k zapouzdøení hardwaru, ale také z dùvodu efektnìjší prezentace funkènosti celého zaøízení. Ruka drží na podstavci pomocí kvalitního suchého zipu, ze kterého se ruka v pøípadì potøeby jednoduše uvolní. Na boèní stranì podstavce jsou konektory, které slouží pro jednoduché a rychlé pøipojení servomotorù k celému systému. Kromì konektoru pro serva je dostupný rovnìž konektor pro pøipojení EMG senzorù.

*Obrázek 4.9: Hotová ruka na podstavci*

## 4.6 Využité souèástky
*   Arduino UNO R3
*   InMoov ruka
*   Pololu Micro Maestro 6-channel
*   6xMG995 servo
*   Myoware muscle sensor Advancer Technologies
*   Ag/AgCL elektrody
*   Rotaèní enkodér
*   0.96" OLED displej 128x64 I2C
*   Pasivní bzuèák
*   Li-pol 2250mAh 7.4V 25C
*   2x10 k? rezistor
*   Napì�ový regulátor na 5V
*   Pøepínaè

*Obrázek 4.10: Schéma zapojení*

---

# ZÁVÌR
Jak už jsem zmínil v úvodu, tak moje práce splnila vìtšinu mých dílèích cílù, jako tøeba bylo sestavení robotické ruky InMoov. Aby byl projekt o nìco více zajímavìjší, tak se mi povedlo pøidat uživatelské rozhraní, které umožòuje 3 zpùsoby ovládaní.

Z dùvodu nedostatkù financi, jsem si nemohl dovolit koupit více EMG senzorù, které by mi umožnily monitorovaní všech prstù. V mojí práci jsem si teda musel vystaèit pouze s jedním, ale i tak jsem s výsledkem sledovaní sevøení a otevøení pìsti velice spokojen.

V prùbìhu jsem narazil na øadu problémù, díky kterým jsem si rozšíøil znalosti v elektrotechnice a programovaní mikrokontroleru. Nejvìtší problém byl výkon mikrokontroleru. Vzhledem k tomu, že už jde takøka o real-time aplikaci, poohlížel jsem se i po nìjakých procesorech s architekturou ARM. Nejlepším adeptem byl Arduino DUE, ale jeho nevýhodou byla vysoká cena. Nakonec jsem se rozhodl sáhnout po absolutním výkonnostním minimu, koupit Arduino UNO, a to hlavnì díky jeho nízké cenì a vyšší vzorkovací frekvenci na A/D pøevodníku, která èiní 9600 Hz a doporuèuje se pøi použití s EMG senzory. Bohužel i tak ho ženu na úplný okraj výkonnosti; musel jsem proto pøizpùsobit kód, abych ušetøil co nejvíce pamìti RAM.

Projekt má stále mnoho prostoru pro rùzná vylepšení, jak už u mechanické ruky samotné, jako tøeba zlepšit napnutí provázkù, aby byli pohyby prstù co nejlepší nebo vylepšit kód pro ovládaní ruky s EMG a taky samotné snímaní EMG, nebo taky vylepšit podstavec a uživatelské rozhraní.

Do budoucna bych se možná chtìl k tomuto projektu a docílit snímaní všech jednotlivých prstù a aby celý program bìžel na ARM procesoru.

---

# SEZNAM POUŽITÝCH INFORMAÈNÍCH ZDROJÙ

1.  History, Travel, Arts, Science, People, Places Smithsonian Magazine. History, Travel, Arts, Science, People, Places Smithsonian Magazine [online]. Copyright © 2021 Smithsonian Magazine [cit. 25.12.2021]. Dostupné z: https://www.smithsonianmag.com/smart-news/study-reveals-secrets-ancient-cairo-toe180963783/.
2.  Ancient Origins. Ancient Origins | Reconstructing the story of humanity's past [online]. Copyright © 2013 [cit. 25.12.2021]. Dostupné z: https://www.ancient-origins.net/history-famous-people/16thcentury-prosthetic-iron-hand-story-gotz-von-berlichingen-006153
3.  Arduino Fast(er) Sampling Rate. Wildan's Blog [online]. Copyright © 2017 [cit. 25.12.2021]. Dostupné z: https://blog.wildan.us/2017/11/03/arduino-fast-er-sampling-rate/
4.  Skeletal muscle structure and function – Musculoskeletal Genetics. Newcastle University Blogging Service [online]. Dostupné z: https://blogs.ncl.ac.uk/katarzynapirog/skeletal-muscle-structure-and-function/
5.  16th Century Prosthetic Iron Hand: The Story of Gotz von Berlichingen | Ancient Origins. Ancient Origins | Reconstructing the story of humanity's past [online]. Copyright © 2013 [cit. 25.12.2021]. Dostupné z: https://www.ancient-origins.net/history-famous-people/16th-century-prosthetic-iron-hand-story-gotz-von-berlichingen-006153
6.  Upper Limb Prostheses | Encyclopedia.com. Encyclopedia.com | Free Online Encyclopedia [online]. Copyright © 2019 [cit. 25.12.2021]. Dostupné z: https://www.encyclopedia.com/medicine/encyclopedias-almanacs-transcripts-and-maps/upper-limb-prostheses
7.  Timeline: Prosthetic Limbs Through the Years | UPMC HealthBeat. Expert Health Information and Articles | UPMC HealthBeat [online]. Dostupné z: https://share.upmc.com/2015/03/timeline-prosthetic-limbs-years/
8.  The Usefulness of Mean and Median Frequencies in Electromyography Analysis | IntechOpen. IntechOpen - Open Science Open Minds | IntechOpen [online]. Copyright © 2012 The Author [cit. 25.12.2021]. Dostupné z: https://www.intechopen.com/chapters/40123
9.  Hand and Forarm – InMoov. InMoov – open-source 3D printed life-size robot [online]. Dostupné z: http://inmoov.fr/hand-and-forarm/
10. How I Designed & Built a Prosthetic Arm - YouTube. YouTube [online]. Copyright © 2021 Google LLC [cit. 25.12.2021]. Dostupné z: https://www.youtube.com/watch?v=CIqzeBxkRws&list=PLYJ6xc5oEtviBMOvdvupa6gBtBWiD_kFk&ab_channel=MahdiDesigns
11. [online]. Dostupné z: https://www.science.org/doi/10.1126/scirobotics.aaw6339
12. Advancer Technologies, LLC: MyoWare Muscle Sensor. Advancer Technologies, LLC [online]. Dostupné z: http://www.advancertechnologies.com/p/myoware.html
13. [online]. Dostupné z: https://www.ncbi.nlm.nih.gov/pmc/articles/PMC3214794/
14. Electromyography (EMG) | Johns Hopkins Medicine. Johns Hopkins Medicine, based in Baltimore, Maryland [online]. Copyright © [cit. 25.12.2021]. Dostupné z: https://www.hopkinsmedicine.org/health/treatment-tests-and-therapies/electromyography-emg
15. Pololu Maestro Servo Controller User’s Guide. Pololu Robotics and Electronics [online]. Copyright © 2001 [cit. 25.12.2021]. Dostupné z: https://www.pololu.com/docs/0J40
16. Základy sportovní kineziologie | Fakulta sportovních studií. Informaèní systém [online]. Dostupné z: https://is.muni.cz/do/1451/e-learning/kineziologie/elportal/pages/funkce_svalu.html
17. Šlacha – Wikipedie. [online]. Dostupné z: https://cs.wikipedia.org/wiki/%C5%A0lacha
18. Myofibrila – WikiSkripta. [online]. Dostupné z: https://www.wikiskripta.eu/w/Myofibrila
19. Akèní potenciál – Wikipedie. [online]. Dostupné z: https://cs.wikipedia.org/wiki/Akèní_potencíal
20. Pictorial outline of the decomposition of the surface EMG signal into... | Download Scientific Diagram. ResearchGate | Find and share research [online]. Copyright © 2008 [cit. 25.12.2021]. Dostupné z: https://www.researchgate.net/figure/Pictorial-outline-of-the-decomposition-of-the-surface-EMG-signal-into-its-constituent_fig1_6886902
21. Electromyography with MyoWare Muscle Sensor & Arduino. How To Electronics | Engineering Projects & Tutorials [online]. Copyright © Copyright 2021, All Rights Reserved [cit. 25.12.2021]. Dostupné z: https://how2electronics.com/electromyography-emg-with-myoware-muscle-sensor-arduino/

---

# SEZNAM PØÍLOH

*   Obrázek 1.1 https://www.smithsonianmag.com/smart-news/study-reveals-secrets-ancient-cairo-toe-180963783/
*   obrázek 1.2 https://wellcomecollection.org/works/kyjgqfuh
*   obrázek 1.3 https://commons.wikimedia.org/wiki/File:Berlichingen_Eiserne_Hand_1.jpg
*   obrázek 1.5 https://www.armdynamics.com/our-care/prosthetic-options
*   obrázek 1.6 https://www.ottobock-export.com/en/prosthetics/upper-limb/solution-overview/arm-prostheses-body-powered/
*   obrázek 1.7 https://www.ottobockus.com/prosthetics/upper-limb-prosthetics/solution-overview/myoelectric-prosthetics/
*   obrázek 2.1 https://www.vut.cz/www_base/zav_prace_soubor_verejne.php?file_id=192502
*   obrázek 2.2 https://www.vut.cz/www_base/zav_prace_soubor_verejne.php?file_id=192502
*   obrázek 2.3 https://www.researchgate.net/figure/Pictorial-outline-of-the-decomposition-of-the-surface-EMG-signal-into-its-constituent_fig1_6886902
*   obrázek 2.4 https://how2electronics.com/electromyography-emg-with-myoware-muscle-sensor-arduino/
*   obrázek 3.1 http://www.advancertechnologies.com/p/myoware.html
*   obrázek 3.2 https://www.amazon.com/Humanoid-Fingers-Metal-Manipulator-Servos/dp/B076Q4DYPN
*   obrázek 3.3 http://inmoov.fr/gallery-v2/
