Balner123/GPS_server_NodeJS/docs&LaTex/FINAL_latex/Balner_LOTR_system.tex

% STRUKTURA Z ŠABLONY PRO PSANÍ ZÁVĚREČNÉ STUDIJNÍ PRÁCE
%%%%%%%%%%%%%%%%%%%%%%%%%%%%%%%%%%%%%%%%%%%%
% Autor: Jakub Dokulil (kubadokulil99@gmail.com)

\documentclass[12pt, a4paper,
%oneside,      %% -- odkomentujte, pokud chcete svou práci mít pouze jednostrannou, mezera pro hřbet pak automaticky bude pouze na levé straně
twoside,        %% -- pro oboustranné práce, mezera pro hřbet následně střídá strany.
openright
]{report}

%% Nutné balíčky a nastavení
%%%%%%%%%%%%%%%%%%%%%%%%%%%%

%% Proměnné
\newcommand\obor{INFORMAČNÍ TECHNOLOGIE} %% -- napiš číslo a název tvého oboru
\newcommand\kodOboru{18-20-M/01} %% -- napiš číslo a název tvého oboru
\newcommand\zamereni{se zaměřením na počítačové sítě a programování} %% -- napiš číslo a název tvého oboru
\newcommand\skola{Střední škola průmyslová a umělecká, Opava} %% vyplň název školy
\newcommand\trida{IT4} %% vyplň jméno svého konzultanta
\newcommand\jmenoAutora{Štěpán Balner}  %% vyplň své jméno
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
\titleformat{\chapter}[block]{\scshape\bfseries\LARGE}{\thechapter}{10pt}{\vspace{0pt}}[\vspace{-22pt}]
\titleformat{\section}[block]{\scshape\bfseries\Large}{\thesection}{10pt}{\vspace{0pt}}
\titleformat{\subsection}[block]{\bfseries\large}{\thesubsection}{10pt}{\vspace{0pt}}

\usepackage{tocloft} % Balíček umožní přizpůsobit vzhled tabulky obsahu
\setlength{\cftbeforechapskip}{0pt}  % Menší rozestup pro kapitoly
\setlength{\cftbeforesecskip}{0pt}   % Menší rozestup pro sekce

% Nastavení hloubky číslování a obsahu
\setcounter{secnumdepth}{2} % Číslování až do úrovně 1.1.1
\setcounter{tocdepth}{1}    % Obsah zobrazuje až do úrovně 1.1 (Kapitoly a Sekce)

% Nastavení vzhledu položek v obsahu
\renewcommand{\cftchapfont}{\scshape\bfseries} % Kapitoly: Kapitálky + Tučně
\renewcommand{\cftsecfont}{\scshape}           % Sekce: Kapitálky
\renewcommand{\cftsubsecfont}{\scshape}        % Podsekce: Kapitálky
\renewcommand{\cftsubsubsecfont}{\normalfont}  % Pod-podsekce: Normální písmo (malé)

% Zmenšení mezer pro nejnižší úroveň
\setlength{\cftbeforesubsubsecskip}{-2pt}      % Zmenšená mezera před subsubsection

\usepackage{fancyhdr}
\pagestyle{fancy}
\renewcommand{\headrulewidth}{0.025pt}

\usepackage{booktabs}
\usepackage{array}
\usepackage{tabularx}

\usepackage{url}

%% Balíčky co se můžou hodit :) 
%%%%%%%%%%%%%%%%%%%%%%%%%%%%%%%

\usepackage{pdfpages} %% Balíček umožňující vkládat stránky z PDF souborů, 

\usepackage{upgreek} %% Balíček pro sazbu stojatých řeckých písmen, třeba u jednotky mikrometr. Například stojaté mí: \upmu, stojaté pí: \uppi

\usepackage{amsmath}    %% Balíčky amsmath a amsfonts 
\usepackage{amsfonts}   %% pro sazbu matematických symbolů
\usepackage{esint}     %% pro sazbu různých integrálů (např \oiint)
\usepackage{mathrsfs}
\usepackage{helvet} % Helvet font
\usepackage{mathptmx} % Times New Roman
\usepackage{Oswald} % Oswald font

%% makra pro sazbu matematiky
\newcommand{\dif}{\mathrm{d}} %% makro pro sazbu diferenciálu, místo toho
%% abych musel psát '\mathrm{d}' mi stačí napsat '\dif' což je mnohem 
%% kratší a mohu si tak usnadnit práci

\usepackage{listings}
\usepackage{xcolor}

\renewcommand{\lstlistingname}{Kód}% Listing -> Algorithm
\renewcommand{\lstlistlistingname}{Seznam programových kódů}% List of Listings -> List of Algorithms

\lstalias[]{ES6}[ECMAScript2015]{JavaScript}

% Nastavení barev
% Requires package: color.
\definecolor{mediumgray}{rgb}{0.3, 0.4, 0.4}
\definecolor{mediumblue}{rgb}{0.0, 0.0, 0.8}
\definecolor{forestgreen}{rgb}{0.13, 0.55, 0.13}
\definecolor{darkviolet}{rgb}{0.58, 0.0, 0.83}
\definecolor{royalblue}{rgb}{0.25, 0.41, 0.88}
\definecolor{crimson}{rgb}{0.86, 0.8, 0.24}

\setminted{
  xleftmargin=0.2cm,
  fontsize=\footnotesize,
  baselinestretch=1.0,
  breaklines,
  breakanywhere,
  frame=single,
  framesep=3pt,
  tabsize=2,
  autogobble
}

\lstdefinestyle{JSES6Base}{
	backgroundcolor=\color{white},
	basicstyle=\ttfamily,
	breakatwhitespace=false,
	breaklines=false,
	captionpos=b,
	columns=fullflexible,
	commentstyle=\color{mediumgray}\upshape,
	emph={},
	emphstyle=\color{crimson},
	extendedchars=true,  % requires inputenc
	fontadjust=true,
	frame=single,
	identifierstyle=\color{black},
	keepspaces=true,
	keywordstyle=\color{mediumblue},
	keywordstyle={[2]\color{darkviolet}},
	keywordstyle={[3]\color{royalblue}},
 literate=%
{á}{{\'a}}1 {č}{{\v{c}}}1 {ď}{{\v{d}}}1 {é}{{\'e}}1 {ě}{{\v{e}}}1
{í}{{\'i}}1 {ň}{{\v{n}}}1 {ó}{{\'o}}1 {ř}{{\v{r}}}1 {š}{{\v{s}}}1
{ť}{{\v{t}}}1 {ú}{{\'u}}1 {ů}{{\r{u}}}1 {ý}{{\'y}}1 {ž}{{\v{z}}}1,		
	numbers=left,
	numbersep=5pt,
	numberstyle=\tiny\color{black},
	rulecolor=\color{black},
	showlines=true,
	showspaces=false,
	showstringspaces=false,
	showtabs=false,
	stringstyle=\color{forestgreen},
	tabsize=2,
	title=\lstname,
	upquote=true  % requires textcomp
}

\lstdefinestyle{JavaScript}{
	language=JavaScript,
	style=JSES6Base,
}
\lstdefinestyle{ES6}{
	language=ES6,
	style=JSES6Base
}

%% Začátek dokumentu
%%%%%%%%%%%%%%%%%%%%
\begin{document}
	
	\pagestyle{empty}
	\pagenumbering{Roman}
	
	\cleardoublepage

%% Titulní stránka s informacemi
%%%%%%%%%%%%%%%%%%%%%%%%%%%%%%%%%%%%%%%%
	
	{\fontfamily{phv}\selectfont
		%% Logo školy
		\begin{figure}[h]
			\centering
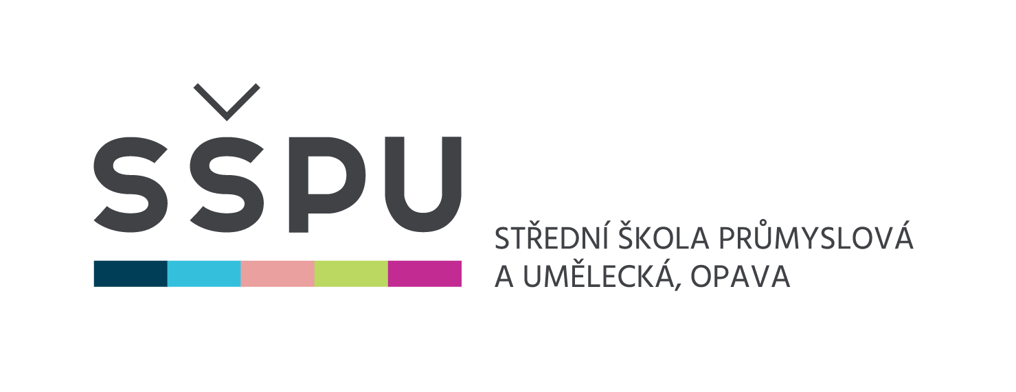
[picture p14: docs&LaTex/FINAL_latex/image/logo-skoly.png]
			 
		\end{figure}

		%% Hlavička práce a její název (viz proměnná \nazev prace)
		%% \sffamily %%% bezpatkové písmo - sans serif
		{\bfseries %%% písmo na stránce je tučně
			\begin{center}
				\vspace{0.025 \textheight}
				\LARGE{ZÁVĚREČNÁ STUDIJNÍ PRÁCE}\\
				\large{dokumentace}\\
				\vspace{0.075 \textheight}
				\LARGE {\nazevPrace}\\
			\end{center}  
		}%%%

		\vspace{1cm}

		\begin{figure}[h]
			\centering
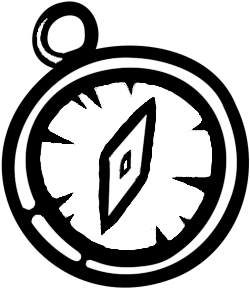
[picture p15: docs&LaTex/FINAL_latex/image/logo_lotr.png]
			 
		\end{figure}

		\vspace{1cm}

		\vspace{0.02 \textheight}
		\begin{table}[h!]
			\begin{tabular}{ll}
				\textbf{Autor:} & \jmenoAutora\\ 
				\textbf{Obor:} & \kodOboru { } \obor\\
				\textbf{} & \zamereni\\
				\textbf{Třída:} & \trida\\
				\textbf{Školní rok:} & \skolniRok\\
			\end{tabular}
			
		\end{table}		
	}
	
\cleardoublepage %% Zalomení dvojstránky
	
%% Stránka obsahující poděkování a prohlášení
%%%%%%%%%%%%%%%%%%%%%%%%%%%%%%%%%%%%%%%%%%%%%%%%%%%%%%%%

%% Poděkování - nepovinné
%%%%%%%%%%%%%%%%%%%%%%%%%%%%
	
	\noindent{\large{\bfseries{Poděkování}\\}}
	\noindent Děkuji Současné době za to, že jsou již LLM (Large Language Models) na urovni takové, kdy kódování tohoto projektu bylo možné i za sníženého nervového vypětí.\\
	
	\vspace*{0.5\textheight} %% Vertikální mezeru je možné upravit

%% Prohlášení - povinné
%%%%%%%%%%%%%%%%%%%%%%%%%%%%
	\noindent{\large{\bfseries{Prohlášení}\\}}  %% uprav si koncovky podle toho na jaký rod se cítíš, vypadá to pak lépe :) 
	\noindent{Prohlašuji, že jsem závěrečnou práci vypracoval samostatně a uvedl veškeré použité 
		informační zdroje.\\}
	\noindent{Souhlasím, aby tato studijní práce byla použita k výukovým a prezentačním účelům na Střední průmyslové a umělecké škole v Opavě, Praskova 399/8.}
	\vfill
	\noindent{V Opavě \datumOdevzdani\\}
	\noindent
	\begin{minipage}{\linewidth}
		\hspace{9.5cm} 
		\begin{tabular}{@{}p{6cm}@{}}
			\dotfill \\
			Podpis autora
		\end{tabular}
	\end{minipage}

	\cleardoublepage %% Zalomení dvojstránky

%% Stránka obsahující abstrakt (anotaci)
%%%%%%%%%%%%%%%%%%%%%%%%%%%%%%%%%%%%%%%%%%%%%%%%%%%%%%%%	

%% Abstrakt v češtině
%%%%%%%%%%%%%%%%%%%%%%%%%%%%
	\noindent{\Large{\bfseries{Abstrakt}\\}}
	\noindent Tato práce obsahuje návrh a realizaci sledovacího systému LOTR (LOcation TRacking System), který se skládá z~fyzického hardwarového zařízení, serverové infrastruktury a~(doplňkově | bonusově | nezávazně) klientské mobilní aplikace.
	
	Hardwarová část je postavena na~platformě ESP32 s~využitím modemu SIMCOM A7670 pro~komunikaci přes sítě LTE a~modulu GPS pro~získávání polohy. Firmware využívá přerušovacího systému a~zápisu dat do~flash paměti. Serverová část, realizovaná v~prostředí Node.js s~databází MySQL, 
	zajišťuje sběr telemetrických dat, správu uživatelů a~poskytuje REST API pro~komunikaci s~koncovými zařízeními. Doplňkovou součástí systému je také nativní aplikace pro~OS Android vyvinutá v~jazyce Kotlin, která slouží jako testovací náhrada hardwarového trackeru.
	
	Výsledkem projektu je prototyp IoT řešení umožňující sledování polohy, historii pohybu a~vzdálenou konfiguraci připojených zařízení.

	\vspace{18pt}
	
	\noindent{\large{\bfseries{Klíčová slova}}}
	
	\noindent GPS, IoT, sledovací systém, ESP32, LTE, Node.js, MySQL, Android, Kotlin, REST API
	
	\vspace{18pt}
	
	%% Abstract in English
%%%%%%%%%%%%%%%%%%%%%%%%%%%%
\noindent{\Large{\bfseries{Abstract}\\}}
\noindent This work presents the design and implementation of the LOTR (LOcation TRacking System), consisting of a physical hardware tracker, a server infrastructure, and (optionally | as a bonus | non-binding) a client mobile application.

The hardware component is built on the ESP32 platform, using the SIMCOM A7670 modem for LTE connectivity and a GPS module for location acquisition. The firmware employs an interrupt-driven approach and writes telemetry to flash memory. The server component, implemented in Node.js with a MySQL database, collects telemetry data, manages users, and exposes a REST API for communication with devices. An additional native Android application written in Kotlin serves as a testing substitute for the hardware tracker.

The outcome is an IoT prototype enabling location tracking, movement history, and remote configuration of connected devices.

\vspace{18pt}

\noindent{\large{\bfseries{Keywords}}}

\noindent GPS, IoT, tracking system, ESP32, LTE, Node.js, MySQL, Android, Kotlin, REST API

\vspace{18pt}

\clearpage %% Page break

%% Stránka s generovaným obsahem
%%%%%%%%%%%%%%%%%%%%%%%%%%%%%%%%%%%%%%%	
	
	\tableofcontents %% Vygeneruje tabulku s obsahem

	\cleardoublepage %% Zarovnání na lichou stranu před začátkem číslování
	\pagenumbering{arabic} %% Nastavení způsobu číslování stránek (alternativy roman | Roman)
	\setcounter{page}{1} %% Nastavení počitadla stránek
	\pagestyle{plain} %% Zapnutí číslování stránek (bez záhlaví)

%% Stránka s úvodem - povinná část
%%%%%%%%%%%%%%%%%%%%%%%%%%%%%%%%%%%%%%%		
	\chapter*{Úvod}
	Můžeme říci, že již od začátku cílem projektu bylo vytvořit kompletní a~hlavně uzavřený systém, co by mohl tzv. "žít svým vlastním životem" a~jehož použití by bylo možné i~v~reálných podmínkách.
	
	Již kdysi jsem se zabýval "sběrnými" nebo "sledovacími" systémy. Po-ohlížel jsem se z~variabilních (různých ale rozhodně ne nelegálních) důvodů po~možnostech jak by šlo sestrojit zařízení schopné nahrávat video a~ukládat na~SD kartu nebo jiné uložiště díky vlastnímu zařízení, protože komerční varianty nesplnovaly požadavky na~velikost. 
	Sledování polohy je jenom dalším krokem v~tomto směru. Možnost že bych měl krabičku, jež bych mohl dát někomu do~auta, připnout k~nápravě kamionu (naivní to myšlenka) nebo vložit do~zásilky a~sledovat jeho pohyb do~doby vybití baterie, byla, a~stále je, velmi přitažlivá.
	
	Bylo jasné, že již existují řešení a~"GPS trackery" jsou běžně dostupné a~velmi dobré kvality a~výdrže baterie. Avšak protože jsem dumal nad tématem pro~zavěrečný projekt, výroba a~řešení konstrukce vlastního, sic nízkokvalitního a~nutně dosti poruchového, zařízení se ukázal jako vhodný nápad.
	Existovala možnost vytvořit opravdu pouze "krabici" trackeru s~ukládáním dat na~pevné úložiště , avšak rozhodl jsem se to spojit s~vývojem serveru jež by umožňoval sledování v~reálném čase. Na~tomto "webovém" serveru by tak šlo zobrazovat a~spravovat data posílaná  zařízením přes mobilní síť.  
	To se pak přirozeně rozvinulo do~plného systému s~uživatelskými účty a~možností spravovat více zařízení na~jednom z~nich. 

	Jako méně důležitou, spíše doplňkovou, ale přesto užitečnou součást systému jsem pak viděl výtvoření mobilní aplikace pro~systém Android. Avšak z~důvodu, že by pak byl projekt roztřepen na~až mnoho frontách, věnoval jsem ji menší (spíše minimální) pozornost.
	Tato aplikace nemá důležitosti jako ostatní komponenty, jelikož byla koncipována jako testování API a~pro~neznalost Kotlinu většina (přes 90~\%) jejího kódu byla generována LLM (chcete-li "AI", konkrétně Gemini).
	Tato dokumentace ji proto nezmiňuje, pouze popisuje uivatelské prostředí.

	Proto je tento Dokument rozdělen do~tří hlavních kapitol. 

\begin{enumerate}
	  \setlength\itemsep{0.2em}
  \setlength\parskip{0pt}
  \setlength\parsep{0pt}
	\item kapitola popisuje samotné zařízení, jeho návrh a~konstrukci i~príklady použití.
	\item kapitola popisuje kód serveru, jeho návrh, API a~většinu možností uživatelského rozhraní.
	\item kapitola v~krátkosti popisuje Aplikaci pro~Android a~její uživatelské rozhraní.
\end{enumerate}

%Příkaz \chapter*{Úvod}	
%Tento příkaz vytvoří novou kapitolu s názvem "Úvod" ve vašem dokumentu.
%Hvězdička * u příkazu \chapter* znamená, že tato kapitola nebude mít číslo. Ve výsledném dokumentu se tedy objeví jako "Úvod" bez předcházejícího čísla kapitoly, které se obvykle zobrazuje u číslovaných kapitol.
%Tento příkaz také znamená, že kapitola se automaticky neobjeví v obsahu, protože LaTeX standardně zahrnuje do obsahu pouze číslované kapitoly.
%\addcontentsline{toc}{chapter}{Úvod}
%Tento příkaz ručně přidává záznam do obsahu.
%První parametr toc označuje, že přidáváme záznam do Table of Contents (obsahu).
%Druhý parametr chapter specifikuje úroveň záznamu. V tomto případě říkáme, že přidávaný záznam má být považován za kapitolu.
%Třetí parametr Úvod je text, který se objeví v obsahu. V tomto případě bude v obsahu zobrazen název "Úvod".	

%Tipy k psaní úvodu
%Je povinný, nadpis neměňte, rozsah - max. 1 strana. 
%Tato část práce obsahuje: 
%* náhled do řešené problematiky, zdůvodnění volby problematiky, 
%* předem definované cíle práce, 
%* motivaci pro další čtení textu včetně stručného uvedení obsahu následujících kapitol 

\include{chapter_1_hw}
\include{chapter_2_server}
\include{chapter_3_apk_v2}
	
\chapter*{Závěr}

\noindent Dokončeno, v~přijatelné míře a~rozsahu, bylo samotné jádro systému. I~když bez pokročilého zabezpečení tak API funguje a~zařízení dokáží se~serverem komunikovat a~mají schopnosti se~tak či onak vypořádat s~vypadky sítě (cachování)
a~HW-tracker přestože s~obtížemi by přece jenom šlo do~doby vybití baterie používat v~rámci možností (přes snahy o~nízkou spotřeby však výdrž není úplně optimální). Nejlépe asi použít jako GPS alarm, kdy by se tracker hlasil s~periodou cca.~1~dne a~v~případě změny by uživatel dostal hlášení. 
\noindent Celkově tedy systém funguje v~urovni možností a~schopností prototypu, ale je zde mnoho místo pro~zlepšení a~rozšíření.

\noindent Seznam nedokonalostí či nedodělků může být dosti dlouhý. Jako hlavní nedostatek vidím absenci 3D tisknutého pouzdra pro~HW tracker. Jediná použitelná část z~již zmíněného modelu zůstal držák na~: baterii a~její nabíječku, ten se ukázal jako užitečný pro~jednoduší manipulací s~celou kontrukcí.
Dále také celý základní princip API a~identifikace mezi zařízeními a~serverem je dosti primitivní a~náchylný k~chybám. V~budoucnu by bylo vhodné přejít na~nějaký propracovanější systém autentizace a~autorizace zařízení (možná MQTT mezi-server obstarávající autentifikaci ?), místo pouhého ID a~uživatelských údajů ( je to takto dosti jednoduché na~falšování požadavků).
Také nějaké více komplikované možnosti výpisu či třídění dat v~uživatelském rozhraní chybí, a~tak bych mohl pokračovat\dots
To vše je tak v~možnostech dalšího rozšíření a~možných budoucích vylepšeních.

\vspace*{2cm}
\noindent Odkaz na GitHub repozitář projektu : \url{https://github.com/Balner123/GPS_server_NodeJS}

\addcontentsline{toc}{chapter}{Závěr}

%\chapter*{Seznam použitých informačních zdrojů}
%\addcontentsline{toc}{chapter}{Seznam použitých informačních zdrojů}
	
	%% literatura
	\begin{thebibliography}{99}
		% Hardware
		\bibitem{espressif_docs} ESPRESSIF SYSTEMS. \textit{ESP32 Technical Reference Manual} [Online]. 2024. Dostupné z: \url{https://www.espressif.com/en/support/documents/technical-documents}
		\bibitem{esp_idf} ESPRESSIF SYSTEMS. \textit{ESP-IDF Programming Guide} [Online]. 2024. Dostupné z: \url{https://docs.espressif.com/projects/esp-idf/en/latest/}
		\bibitem{arduino_esp32} ESPRESSIF SYSTEMS. \textit{Arduino core for the ESP32} [Software]. GitHub, 2024. Dostupné z: \url{https://github.com/espressif/arduino-esp32}
		\bibitem{simcom_at} SIMCOM WIRELESS SOLUTIONS. \textit{A7670 Series AT Command Manual} [Online]. 2022. Dostupné z: \url{https://www.simcom.com/product/A7670E.html}
		\bibitem{simcom_hd} SIMCOM WIRELESS SOLUTIONS. \textit{A7670 Series Hardware Design} [Online]. 2022. Dostupné z: \url{https://www.simcom.com/product/A7670E.html}
		\bibitem{lilygo_tsima7670} LILYGO. \textit{LilyGO T-SIM A7670(E) — ESP32 + LTE Cat-1 Development Board} [Online]. GitHub, 2023. Dostupné z: \url{https://github.com/Xinyuan-LilyGO/LilyGo-T-SIM-A7670}
		\bibitem{ublox_datasheet} U-BLOX AG. \textit{NEO-6 u-blox 6 GPS Modules Data Sheet} [Online]. 2011. Dostupné z: \url{https://content.u-blox.com/sites/default/files/NEO-6_DataSheet_%28GPS.G6-HW-09005%29.pdf}
		\bibitem{ublox_protocol} U-BLOX AG. \textit{u-blox 6 Receiver Description including Protocol Specification} [Online]. 2011. Dostupné z: \url{https://content.u-blox.com/sites/default/files/u-blox6_ReceiverDescriptionProtocolSpec_%28GPS.G6-SW-12013%29_Public.pdf}

		% Firmware (MCU)
		\bibitem{freertos_guide} AMAZON WEB SERVICES. \textit{FreeRTOS Kernel Developer Guide} [Online]. 2024. Dostupné z: \url{https://www.freertos.org}
		\bibitem{tinygsm_repo} SHYMANSKYY, Volodymyr. \textit{TinyGSM: A small Arduino library for GSM/LTE modules} [Software]. GitHub, 2023. Dostupné z: \url{https://github.com/vshymanskyy/TinyGSM}
		\bibitem{tinygpspp} HART, Mikal. \textit{TinyGPS++: NMEA parser for Arduino} [Software]. GitHub, 2023. Dostupné z: \url{https://github.com/mikalhart/TinyGPSPlus}
		\bibitem{arduinojson} BLANCHON, Benoit. \textit{ArduinoJson} [Software]. 2024. Dostupné z: \url{https://arduinojson.org/}

		% Server
		\bibitem{nodejs_docs} OPENJS FOUNDATION. \textit{Node.js Documentation} [Online]. Dostupné z: \url{https://nodejs.org/en/docs/}
		\bibitem{express_docs} EXPRESS. \textit{Express — Node.js web application framework} [Online]. Dostupné z: \url{https://expressjs.com}
		\bibitem{sequelize_manual} SEQUELIZE. \textit{Sequelize v6 Reference Manual} [Online]. Dostupné z: \url{https://sequelize.org}
		\bibitem{mysql_docs} ORACLE. \textit{MySQL Documentation} [Online]. Dostupné z: \url{https://dev.mysql.com/doc/}
		\bibitem{jsonwebtoken} AUTH0. \textit{jsonwebtoken — JWT for Node.js} [Software]. GitHub, 2024. Dostupné z: \url{https://github.com/auth0/node-jsonwebtoken}
		\bibitem{bcryptjs} DcodeIO. \textit{bcrypt.js — bcrypt in JavaScript} [Software]. GitHub, 2024. Dostupné z: \url{https://github.com/dcodeIO/bcrypt.js}
		\bibitem{dotenv} MOTDOTLA. \textit{dotenv — Loads environment variables} [Software]. GitHub, 2024. Dostupné z: \url{https://github.com/motdotla/dotenv}
		\bibitem{cors_mw} EXPRESSJS. \textit{cors — CORS middleware for Express} [Software]. GitHub, 2024. Dostupné z: \url{https://github.com/expressjs/cors}
		\bibitem{oauth2_rfc} IETF. \textit{The OAuth 2.0 Authorization Framework}. RFC 6749. 2012. Dostupné z: \url{https://www.rfc-editor.org/rfc/rfc6749}
		\bibitem{oauth2_bearer} IETF. \textit{The OAuth 2.0 Authorization Framework: Bearer Token Usage}. RFC 6750. 2012. Dostupné z: \url{https://www.rfc-editor.org/rfc/rfc6750}
		\bibitem{jwt_rfc} IETF. \textit{JSON Web Token (JWT)}. RFC 7519. 2015. Dostupné z: \url{https://www.rfc-editor.org/rfc/rfc7519}

		% Mapy a geodata
		\bibitem{leaflet_docs} AGAFONKIN, Vladimir. \textit{Leaflet: an open-source JavaScript library for mobile-friendly interactive maps} [Online]. Dostupné z: \url{https://leafletjs.com}
		\bibitem{osm_legal} OPENSTREETMAP FOUNDATION. \textit{OpenStreetMap — Copyright and License} [Online]. Dostupné z: \url{https://wiki.openstreetmap.org/wiki/Legal_FAQ}
		\bibitem{osm_tile_policy} OPENSTREETMAP FOUNDATION. \textit{Tile Usage Policy} [Online]. Dostupné z: \url{https://operations.osmfoundation.org/policies/tiles/}

		% Šablona a AI asistent
		\bibitem{sablonaSOC} DOKULIL, Jakub. \textit{Šablona pro psaní SOČ v programu \LaTeX} [Online]. Brno, 2020. Dostupné z: \url{https://github.com/Kubiczek36/SOC_sablona}
		\bibitem{gemini_model} GOOGLE DEEPMIND. \textit{Gemini 3: Multimodal Generative AI Model} [Online]. 2025. Asistoval při generování a strukturování dokumentace. Dostupné z: \url{https://deepmind.google/}
	\end{thebibliography}
	
	%% obrázky 
	\listoffigures
	\addcontentsline{toc}{chapter}{Seznam obrázků}
	
	%% tabulky
	\listoftables
	\addcontentsline{toc}{chapter}{Seznam tabulek}
	
	%\appendix %% začínají přílohy
	%\addcontentsline{toc}{chapter}{Přílohy}
	%\titleformat{\chapter}[block]{\scshape\bfseries\LARGE}{Příloha \thechapter}{10pt}{\vspace{0pt}}[\vspace{-22pt}] %% nastavení nadpisu u příloh

\end{document}
