Balner123/GPS_server_NodeJS/docs&LaTex/FINAL_latex/Balner_LOTR_system.pdf

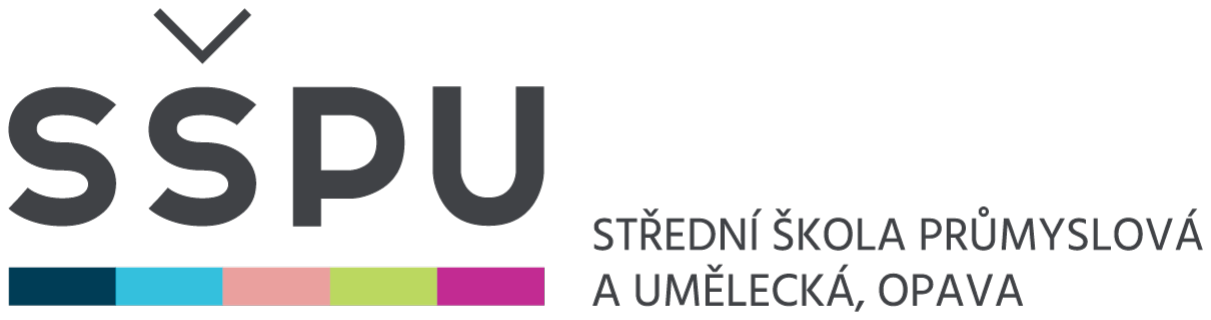
[picture p37: figure]

# ZÁVERE ˇ CNÁ STUDIJNÍ PRÁCE ˇ

### dokumentace

# LOTR - LOcation TRacking System

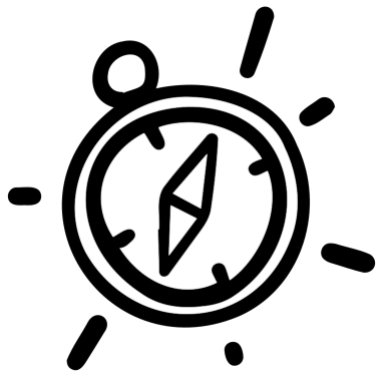
[picture p38: figure]

Autor: | Štepán Balner ˇ
Obor: | 18-20-M/01 INFORMACNÍ TECHNOLOGIE ˇ
se zameˇˇrením na pocíta ˇ cové sít ˇ | e a programování ˇ
Trída: ˇ | IT4
Školní rok: 2025/26

### Podekování ˇ

Dekuji t ˇ | em, jimž pod ˇ | ekováno nebylo. ˇ

### Prohlášení

Prohlašuji, že jsem závere ˇ cnou práci vypracoval samostatn ˇ | e a uvedl veškeré použité informa ˇ | cní ˇ
zdroje.
Souhlasím, aby tato studijní práce byla použita k výukovým a prezentacním ú ˇ | cel˚um na St ˇ | ˇrední
pr˚umyslové a umelecké škole v Opav ˇ | e, Praskova 399/8. ˇ

V Opave 1. 1. 2026 ˇ
Podpis autora

## Anotace

Cílem této práce je návrh a realizace sledovacího systému LOTR (LOcation TRacking System), který se skládá z fyzického hardwarového zaˇrízení, serverové infrastruktury a klientské mobilní aplikace.

Hardwarová cást je postavena na platform ˇ | e ESP32 s využitím modemu SIMCOM A7670 ˇ
pro komunikaci pˇres síte LTE a modulu GPS pro získávání polohy. Firmware je optimalizován ˇ
pro nízkou spotˇrebu energie a spolehlivý pˇrenos dat. Serverová cást, realizovaná v prost ˇ | ˇredí
Node.js s databází MySQL, zajišt’uje sber telemetrických dat, správu uživatel˚u a poskytuje ˇ REST API pro komunikaci s koncovými zaˇrízeními. Soucástí systému je také nativní aplikace ˇ pro OS Android vyvinutá v jazyce Kotlin, která slouží jako plnohodnotná softwarová náhrada hardwarového trackeru.
Výsledkem projektu je funkcní prototyp IoT ˇ | ˇrešení umožnující sledování polohy v reálném ˇ
case, historii pohybu a vzdálenou konfiguraci p ˇ | ˇripojených zaˇrízení.

### Klícová slova ˇ

GPS, IoT, sledovací systém, ESP32, LTE, Node.js, MySQL, Android, Kotlin, REST API

# Obsah

ÚVOD | | 3
1 FYZICKÉ ZARÍZENÍ ˇ | „TRACKER“ | 5
2 SERVEROVÁ CÁST ˇ | 7

VI

2.4.2 ALGORITMY PRO ZPRACOVÁNÍ POLOHY (GEOFENCING, CLUSTERING) | 8
3 APLIKACE PRO ANDROID | 9
3.2.1 JAZYK KOTLIN A ASYNCHRONNÍ PROGRAMOVÁNÍ (COROUTINES) . | 9
3.2.2 SYSTÉMOVÉ KOMPONENTY (FOREGROUND SERVICE, WORKMANAGER) | 9
3.2.4 ZABEZPECENÉ ÚLOŽIŠT ˇ | Eˇ (ENCRYPTEDSHAREDPREFERENCES) . . . | 9
3.3.1 VRSTEVNATÁ ARCHITEKTURA A REAKTIVNÍ MODEL (STATEFLOW) . | 9
3.4.3 Rˇ ÍZENÍ SPOTREBY A VZDÁLENÉ VYPÍNÁNÍ ˇ | (POWERCONTROLLER) . | 10
ZÁVERˇ | | 11
SEZNAM POUŽITÝCH INFORMACNÍCH ZDROJ ˇ | U˚ | 13
SEZNAM OBRÁZKU˚ | | 15
SEZNAM TABULEK | | 15
PRÍLOHY ˇ | | 15
A SCHÉMA ZAPOJENÍ HARDWARE | | 17
B ER DIAGRAM DATABÁZE | | 19
C UŽIVATELSKÝ MANUÁL APLIKACE | | 21

## ÚVOD

M˚užeme ˇríci, že již od zacátku cílem projektu bylo vytvo ˇ | ˇrit kompletní a hlavne uzav ˇ | ˇrený sys-

tém, co by mohl žít svým vlastním životem a jehož použití by bylo možné nasadit v reálných podmínkách.

Již kdysi jsem se zabýval "sbernými"nebo "sledovacími"systémy. Poohlížel jsem se z varia- ˇ bilních d˚uvod˚u po možnostech jak by šlo sestrojit zaˇrízení schopné nahrávat video a ukládat na
SD kartu nebo jiné uložište. Sledování polohy je jenom dalším krokem v tomto sm ˇ | eru. Možnost ˇ
že bych mel krabi ˇ | cku jež bych mohl dát n ˇ | ekomu do auta, nebo jej p ˇ | ˇripnout k náprave kamionu ˇ
a sledoval jeho pohyb do doby vybití baterie byla, a stále je, velmi pˇritažlivá.

Bylo jasné, že již existují ˇrešení a "GPS-trackery"jsou bežn ˇ e dostupné a velmi dobré kva- ˇ lity a výdrže baterie. Avšak protože jsem dumal nad tématem pro zavere ˇ cný projekt, výroba a ˇ ˇrešení konstrukce vlastního, sic nízkokvalitního a dosti poruchového, zaˇrízení se ukázal jako vhodný nápad. Existovala možnost vytvoˇrit opravdu pouze "krabici"trackeru s ukládáním dat n
apevné úložište , avšak rozhodl jsem se to spojit s vývojem serveru jež by umož ˇ | noval sledování ˇ
v reálném case. Na tomto "webovém"serveru by tak šlo zobrazovat a spravovat data posílaná ˇ zaˇrízením pˇres mobilní sít’. To se pak pˇrirozene rozvinulo do plného systému s uživatelskými ˇ
úcty a možností spravovat více za ˇ | ˇrízení na jednom z nich. Již z pocátk˚u pak bylo také na vý- ˇ
ledni ,že pokud by server mel fungovat a p ˇ | | ˇrijímat data spolehlive, tak jeho jádrem by muselo ˇ
být responzivní a hlavne "robustní"API. Jeho struktura se však, hlavn ˇ | e kv˚uli postupnému p ˇ | ˇre-
hodnocuvání principu komunikace mezi serverem a zaˇrízeními, dosti drasticky menila. Fyzické ˇ zaˇrízení totiž bylo hlavním pilíˇrem celého systému a jeho kontrukce, složení, a hlavne samotný ˇ kod, udávaly smer vývoje všeho ostatního. ˇ
Jako méne d˚uležitou, ale p ˇ | ˇresto užitecnou sou ˇ | cást systému jsem pak vid ˇ | el soub ˇ | ežný vývoj ˇ
mobilní aplikace pro systém Android. Ta mela sloužit jako plnohodnotná náhrada hardwarového ˇ zaˇrízení a možná jako náhrada více schopná.

3

1 FYZICKÉ ZARÍZENÍ ˇ | „TRACKER“

### 1.1 TEORETICKÁ VÝCHODISKA A POUŽITÉ TECHNOLOGIE

### 1.1.1 Mikrokontroléry a SoC (ESP32)

### 1.1.2 Mobilní komunikace v IoT a AT príkazy ˇ

### 1.1.3 Globální navigacní systémy (GPS) ˇ

1.1.4 Operacní systémy reálného ˇ | casu (FreeRTOS) ˇ

### 1.1.5 Principy rízení napájení (Power Latch) ˇ

### 1.2 NÁVRH HARDWARE

### 1.2.1 Výber komponent (LilyGO, NEO-6M) ˇ

### 1.2.2 Schéma zapojení a periferie

### 1.3 IMPLEMENTACE FIRMWARE

### 1.3.1 Architektura a použité knihovny

1.3.2 Rízení spot ˇ | reby a pracovní cyklus ˇ

### 1.3.3 Správa datového úložište (LittleFS) ˇ

### 1.4 KOMUNIKACE A DATA

1.4.1 Komunikacní protokol a zabezpe ˇ | cení ˇ

5

### 1.4.2 Struktura dat a handshake

### 1.5 KONFIGURACE A SERVISNÍ REŽIM

### 1.5.1 OTA režim a webové rozhraní

### 1.5.2 Parametrizace zarízení ˇ

## 2 SERVEROVÁ CÁST ˇ

### 2.1 ÚVOD A KONCEPCE SYSTÉMU

### 2.1.1 Role serveru v systému LOTR

### 2.1.2 Monolitická architektura a MVC vzor

### 2.2 POUŽITÉ TECHNOLOGIE

### 2.2.1 Runtime prostredí Node.js a framework Express ˇ

### 2.2.2 Relacní databáze a ORM (MySQL + Sequelize) ˇ

### 2.2.3 Principy autentizace a OAuth 2.0

### 2.2.4 REST API architektura

### 2.3 NÁVRH A ARCHITEKTURA BACKENDU

### 2.3.1 Databázové schéma a modely

### 2.3.2 Struktura API endpoint˚u

### 2.3.3 Bezpecnostní mechanismy ˇ

### 2.4 IMPLEMENTACE KLÍCOVÝCH FUNKCÍ ˇ

### 2.4.1 Príjem a validace telemetrických dat ˇ

### 2.4.2 Algoritmy pro zpracování polohy (Geofencing, Clustering)

7

### 2.4.3 Správa uživatel˚u a oprávnení ˇ

2.5 PREZENTACNÍ VRSTVA ˇ | (FRONTEND)

### 2.5.1 Šablonovací systém EJS

### 2.5.2 Vizualizace dat a mapové podklady

## 3 APLIKACE PRO ANDROID

### 3.1 KONCEPT A CÍLE APLIKACE

### 3.1.1 Náhrada hardwarového trackeru

### 3.1.2 Princip Offline-First a odolnost proti výpadk˚um

### 3.2 POUŽITÉ TECHNOLOGIE A PLATFORMA

### 3.2.1 Jazyk Kotlin a asynchronní programování (Coroutines)

### 3.2.2 Systémové komponenty (Foreground Service, WorkManager)

### 3.2.3 Lokální persistence (Room Database)

3.2.4 Zabezpecené úložišt ˇ | e (EncryptedSharedPreferences) ˇ

### 3.3 ARCHITEKTURA APLIKACE

### 3.3.1 Vrstevnatá architektura a reaktivní model (StateFlow)

### 3.3.2 Vlastní implementace HTTP klienta

### 3.4 IMPLEMENTACE KLÍCOVÝCH FUNKCÍ ˇ

### 3.4.1 Sber polohy na pozadí (LocationService) ˇ

### 3.4.2 Dávková synchronizace dat (SyncWorker)

3.4.3 Rízení spot ˇ | reby a vzdálené vypínání (PowerController) ˇ

9

### 3.4.4 Handshake protokol a konfigurace

### 3.5 UŽIVATELSKÉ ROZHRANÍ

### 3.5.1 Hlavní ovládací panel (Dashboard)

### 3.5.2 Diagnostická konzole pro terénní testování

## ZÁVERˇ

### ZHODNOCENÍ PROJEKTU

### MOŽNOSTI BUDOUCÍHO VÝVOJE

11

SEZNAM POUŽITÝCH INFORMACNÍCH ZDROJ ˇ | U˚

13

## LITERATURA

[1] DOKULIL Jakub. Šablona pro psaní SOC v programu L ˇ | ATEX [Online]. Brno, 2020 [cit.

2020-08-24]. Dostupné z: https://github.com/Kubiczek36/SOC_sablona

[2] ESPRESSIF SYSTEMS. ESP32 Technical Reference Manual [Online]. 2024. Dostupné z:

https://www.espressif.com/en/support/documents/technical-documents

[3] SIMCOM. A7600 Series AT Command Manual [Online]. 2021.
[4] JETBRAINS. Kotlin Documentation [Online]. Dostupné z: https://kotlinlang.org/

docs/home.html (https://kotlinlang.org/docs/home.html)

[5] GOOGLE. Android Developers Guides [Online]. Dostupné z: https://developer.

android.com/guide (https://developer.android.com/guide)

# Seznam obrázk˚u

# Seznam tabulek

15

PRÍLOHA ˇ | A SCHÉMA ZAPOJENÍ HARDWARE

17

PRÍLOHA ˇ | B ER DIAGRAM DATABÁZE

19

PRÍLOHA ˇ | C UŽIVATELSKÝ MANUÁL APLIKACE

21
