Balner123/GPS_server_NodeJS/docs&LaTex/docs_server/db_diagrams/Untitled Diagram_2025-11-28T11_33_36.149Z-1.pdf

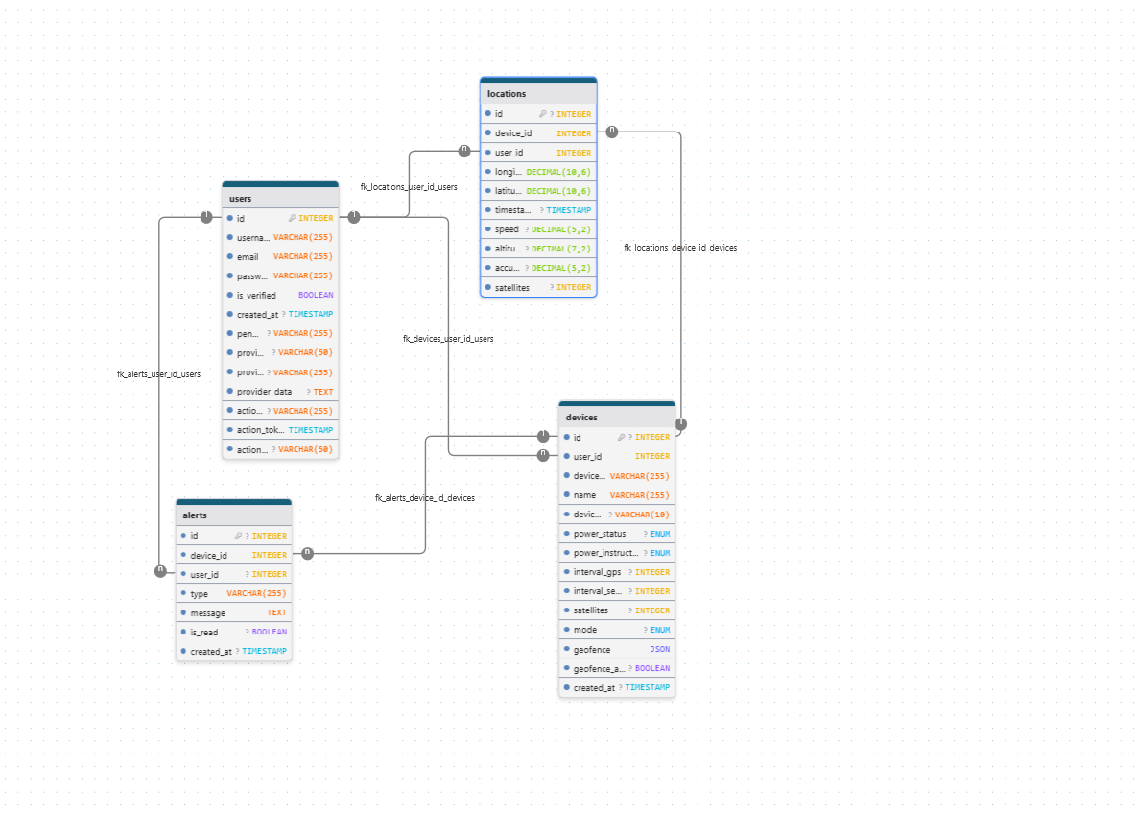
[picture p39: page 1]
