Balner123/GPS_server_NodeJS/docs&LaTex/docs_hw/screenshots/historic#01.webp

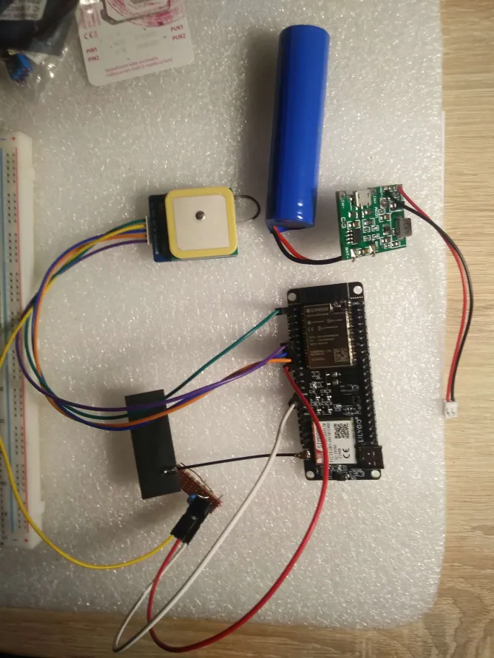
docs&LaTex/docs_hw/screenshots/historic#01.webp
