Balner123/GPS_server_NodeJS/docs&LaTex/docs_hw/screenshots/historic#02.webp

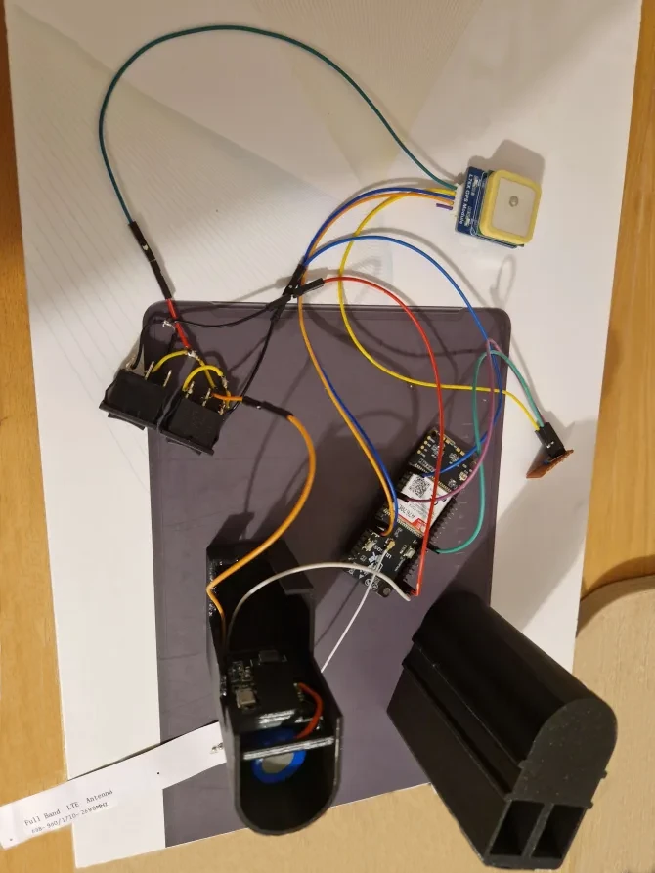
docs&LaTex/docs_hw/screenshots/historic#02.webp
