Balner123/GPS_server_NodeJS/docs&LaTex/docs_server/schemas/sequence_dia_registration_apk.png

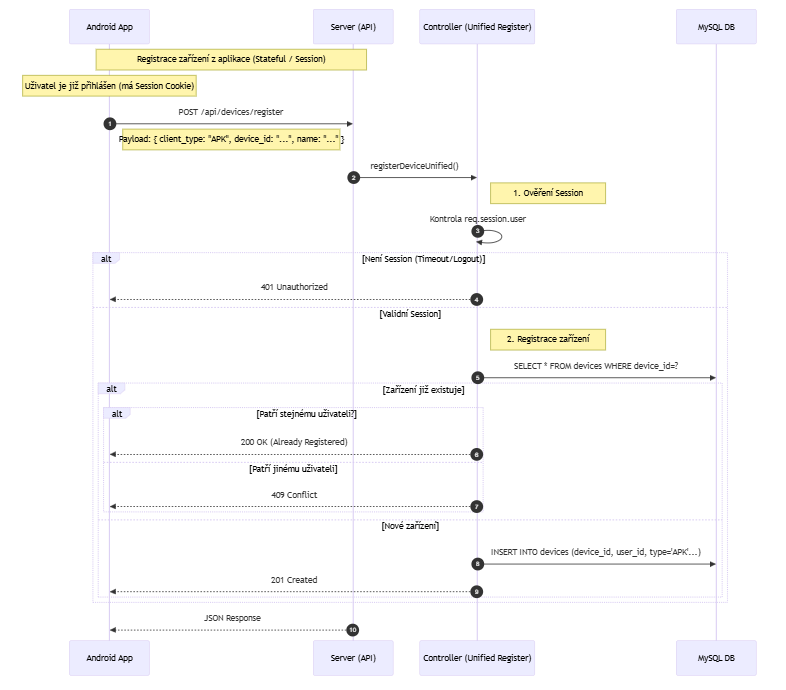
docs&LaTex/docs_server/schemas/sequence_dia_registration_apk.png
