Balner123/GPS_server_NodeJS/docs&LaTex/docs_server/schemas/sequence_dia_registration_hw.png

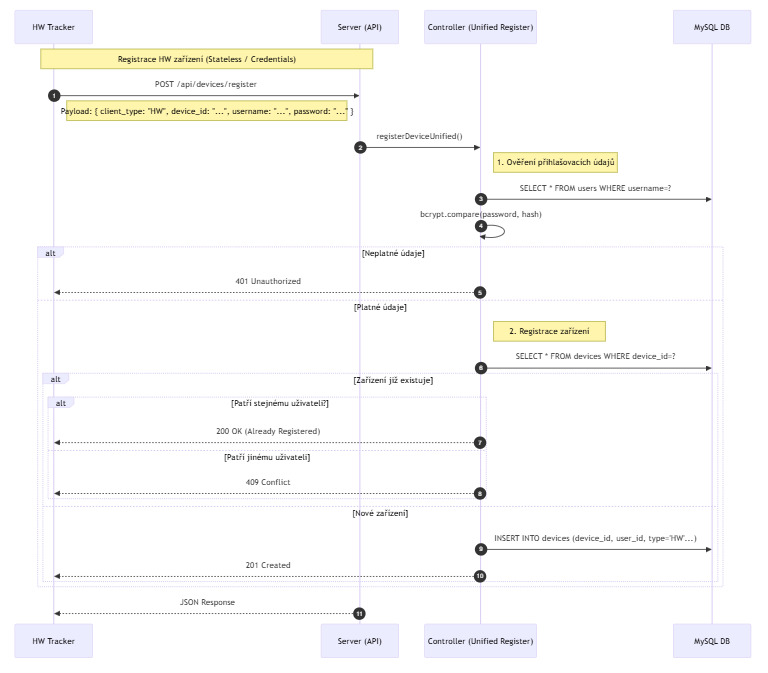
docs&LaTex/docs_server/schemas/sequence_dia_registration_hw.png
