Balner123/GPS_server_NodeJS/docs&LaTex/docs_server/screenshots/alerts_index.png

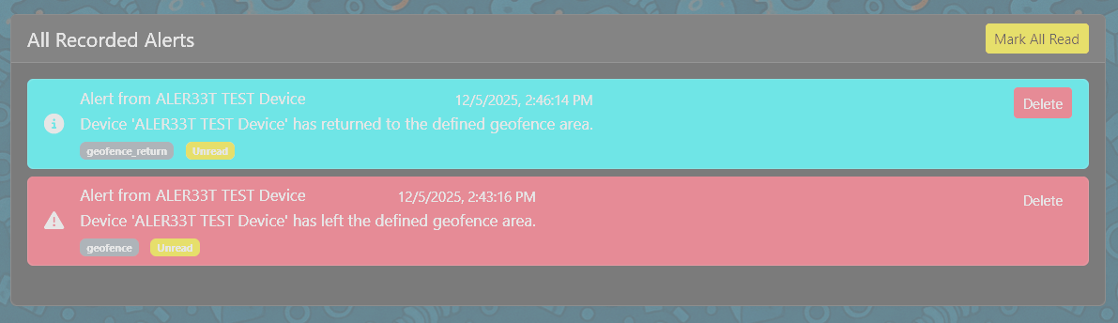
docs&LaTex/docs_server/screenshots/alerts_index.png
