Balner123/GPS_server_NodeJS/docs&LaTex/docs_server/screenshots/authorization_example.png

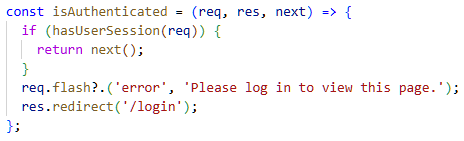
docs&LaTex/docs_server/screenshots/authorization_example.png
