Balner123/GPS_server_NodeJS/docs&LaTex/docs_server/screenshots/composedocker.png

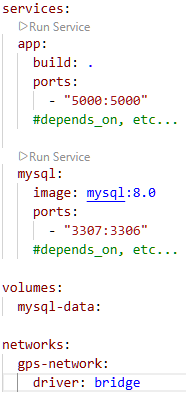
docs&LaTex/docs_server/screenshots/composedocker.png
