Balner123/GPS_server_NodeJS/docs&LaTex/docs_server/screenshots/dockerfile.png

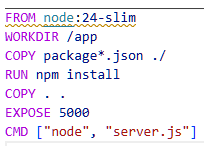
docs&LaTex/docs_server/screenshots/dockerfile.png
