Balner123/GPS_server_NodeJS/docs&LaTex/docs_server/screenshots/index.png

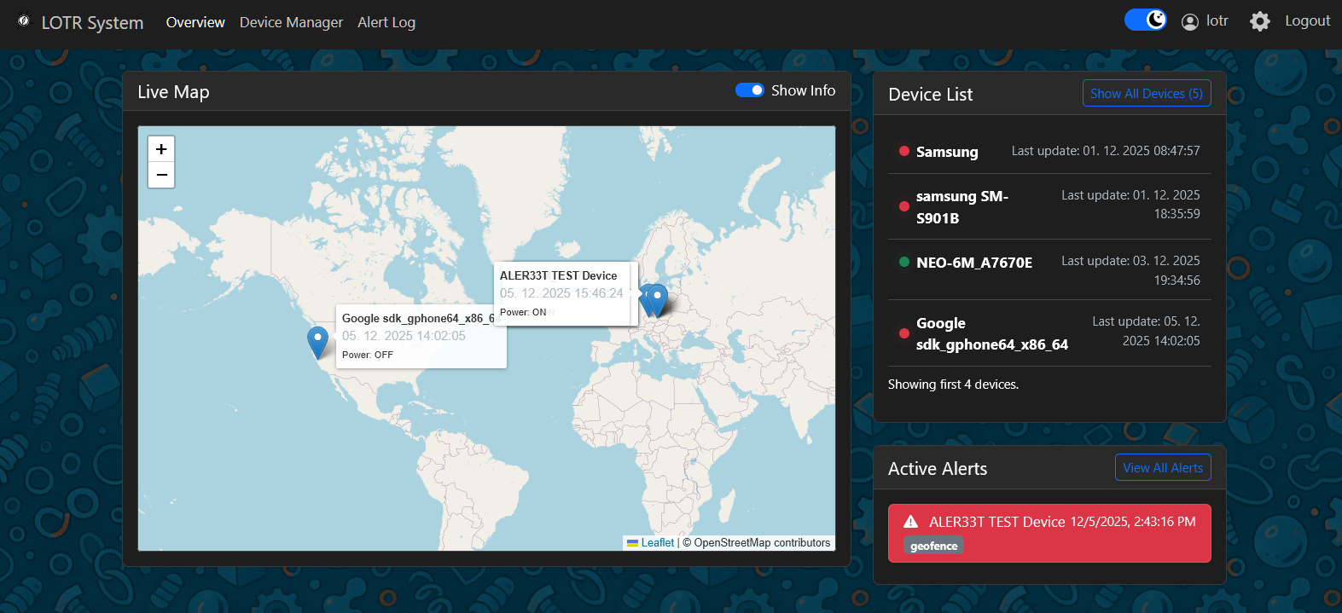
docs&LaTex/docs_server/screenshots/index.png
