Balner123/GPS_server_NodeJS/docs&LaTex/docs_server/screenshots/map.jpg

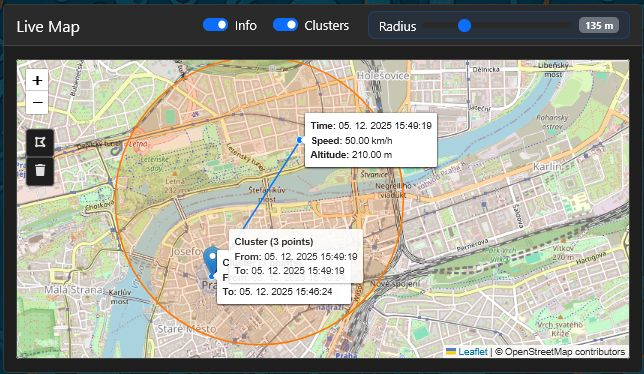
docs&LaTex/docs_server/screenshots/map.jpg
