Balner123/GPS_server_NodeJS/docs&LaTex/docs_server/screenshots/map_init.png

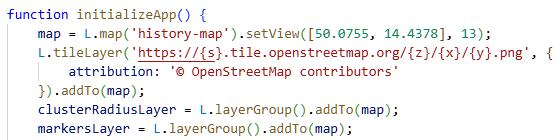
docs&LaTex/docs_server/screenshots/map_init.png
