Balner123/GPS_server_NodeJS/docs&LaTex/docs_server/screenshots/modal#1.png

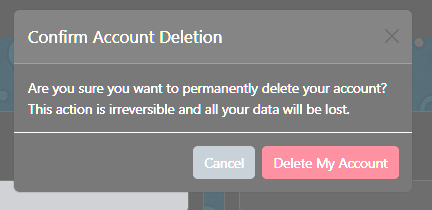
docs&LaTex/docs_server/screenshots/modal#1.png
