Balner123/GPS_server_NodeJS/docs&LaTex/docs_server/screenshots/no-local_strategies.png

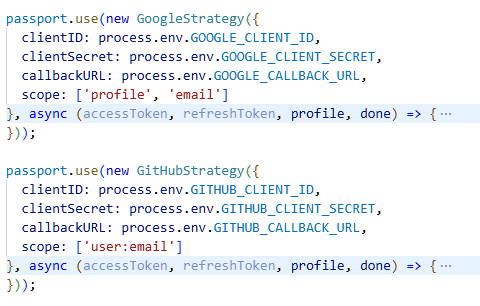
docs&LaTex/docs_server/screenshots/no-local_strategies.png
