Balner123/GPS_server_NodeJS/docs&LaTex/docs_server/screenshots/swagger_docs.png

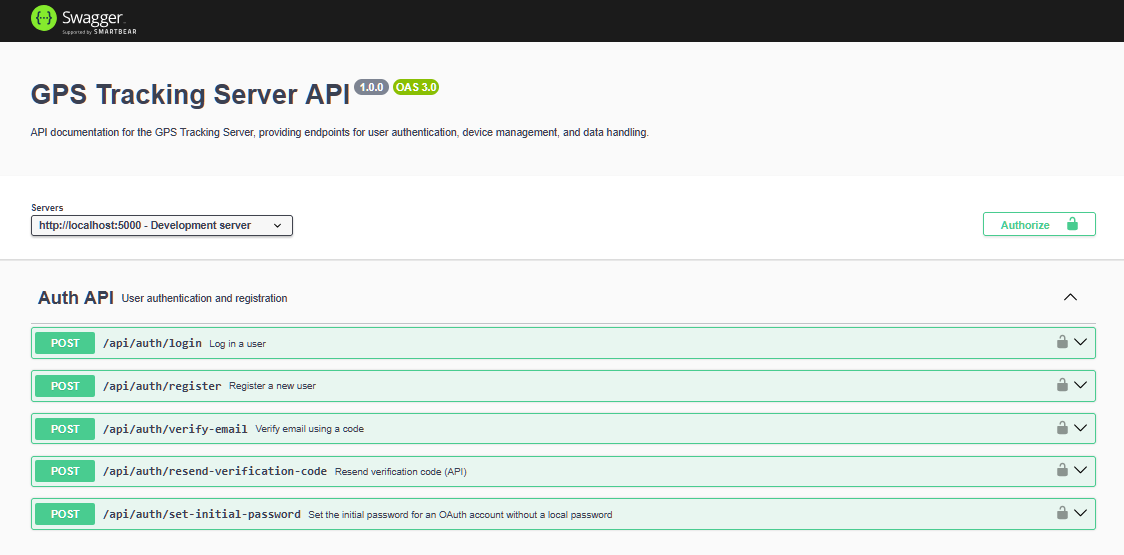
docs&LaTex/docs_server/screenshots/swagger_docs.png
