Balner123/GPS_server_NodeJS/LilyGO-T-A76XX-main/MAIN/FINAL/docs_hw/schemas/life_cycle_states_dia.png

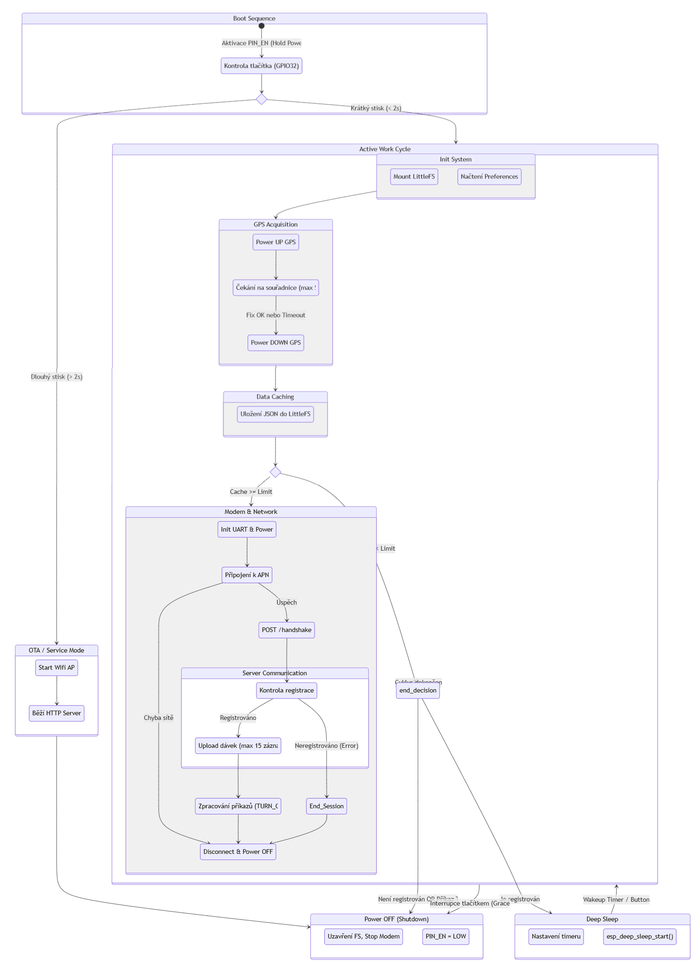
LilyGO-T-A76XX-main/MAIN/FINAL/docs_hw/schemas/life_cycle_states_dia.png
