Balner123/GPS_server_NodeJS/LilyGO-T-A76XX-main/MAIN/FINAL/docs_hw/schemas/process_flow.png

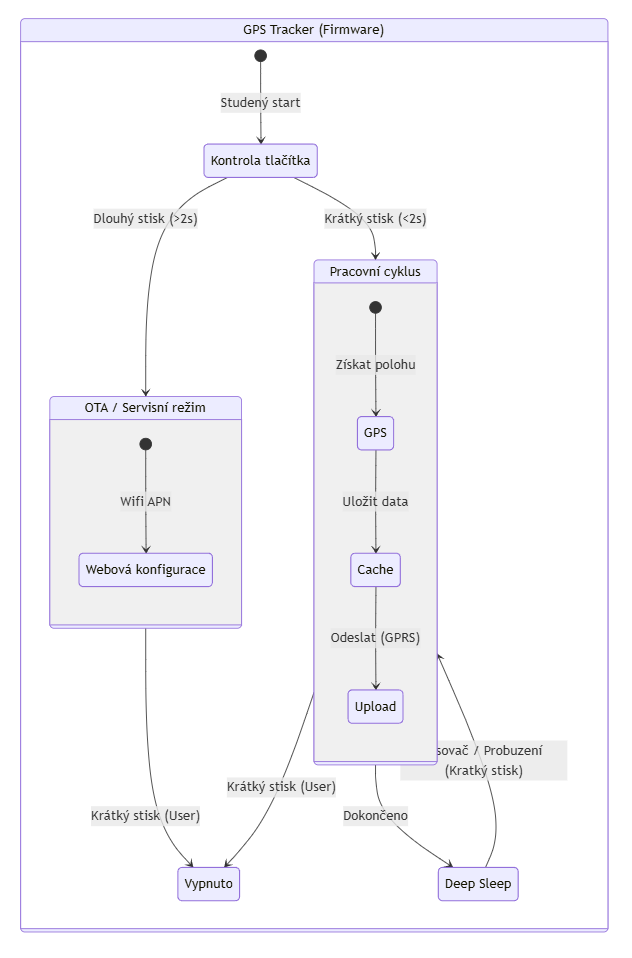
LilyGO-T-A76XX-main/MAIN/FINAL/docs_hw/schemas/process_flow.png
