Balner123/GPS_server_NodeJS/LilyGO-T-A76XX-main/MAIN/FINAL/docs_hw/schemas/schema_POWER_modul.png

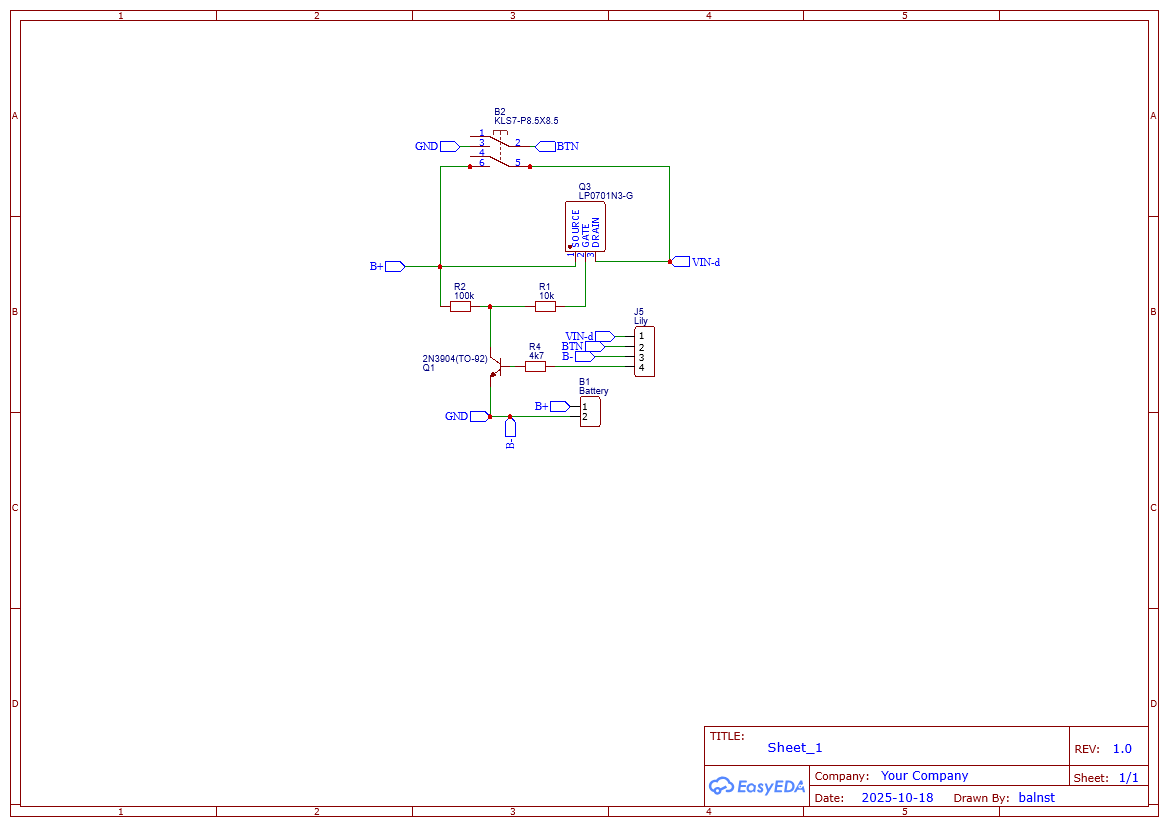
LilyGO-T-A76XX-main/MAIN/FINAL/docs_hw/schemas/schema_POWER_modul.png
