Balner123/GPS_server_NodeJS/LilyGO-T-A76XX-main/MAIN/FINAL/docs_hw/screenshots/deep_sleep.png

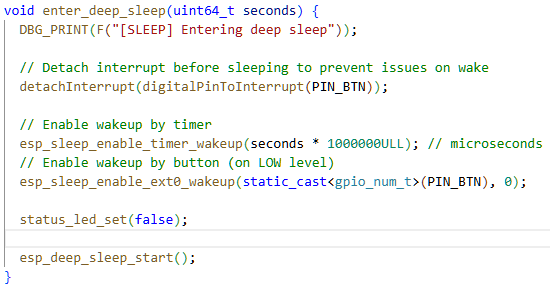
LilyGO-T-A76XX-main/MAIN/FINAL/docs_hw/screenshots/deep_sleep.png
