Balner123/GPS_server_NodeJS/LilyGO-T-A76XX-main/MAIN/FINAL/docs_hw/screenshots/fs_init.PNG

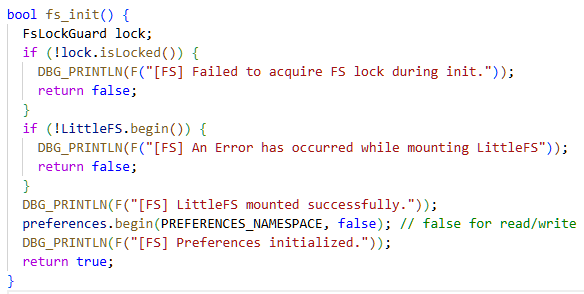
LilyGO-T-A76XX-main/MAIN/FINAL/docs_hw/screenshots/fs_init.PNG
