Balner123/GPS_server_NodeJS/LilyGO-T-A76XX-main/MAIN/FINAL/docs_hw/screenshots/gracefull_shutdown.png

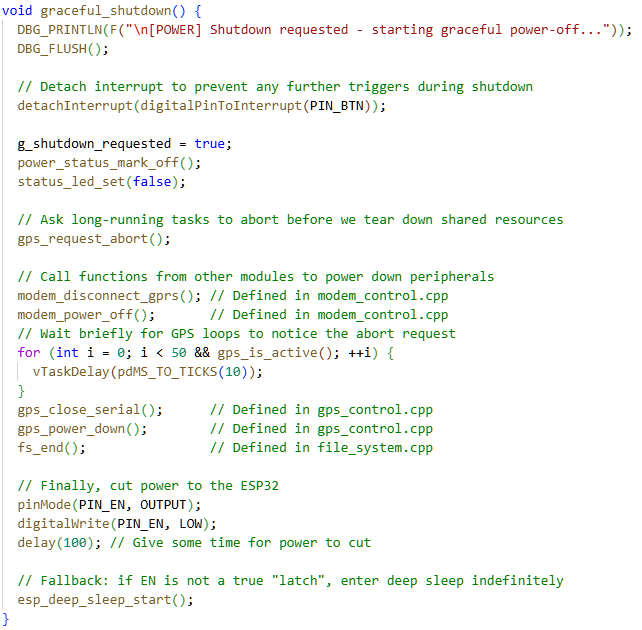
LilyGO-T-A76XX-main/MAIN/FINAL/docs_hw/screenshots/gracefull_shutdown.png
