Balner123/GPS_server_NodeJS/LilyGO-T-A76XX-main/MAIN/FINAL/docs_hw/screenshots/https_session.png

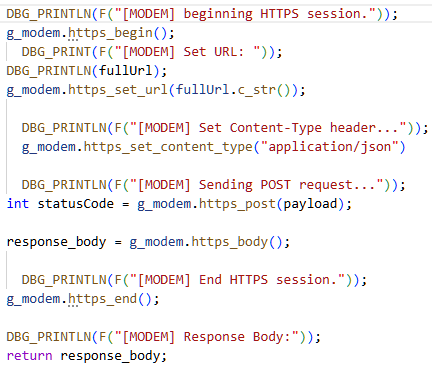
LilyGO-T-A76XX-main/MAIN/FINAL/docs_hw/screenshots/https_session.png
