Balner123/GPS_server_NodeJS/LilyGO-T-A76XX-main/MAIN/FINAL/docs_hw/screenshots/OTA_log_1.png

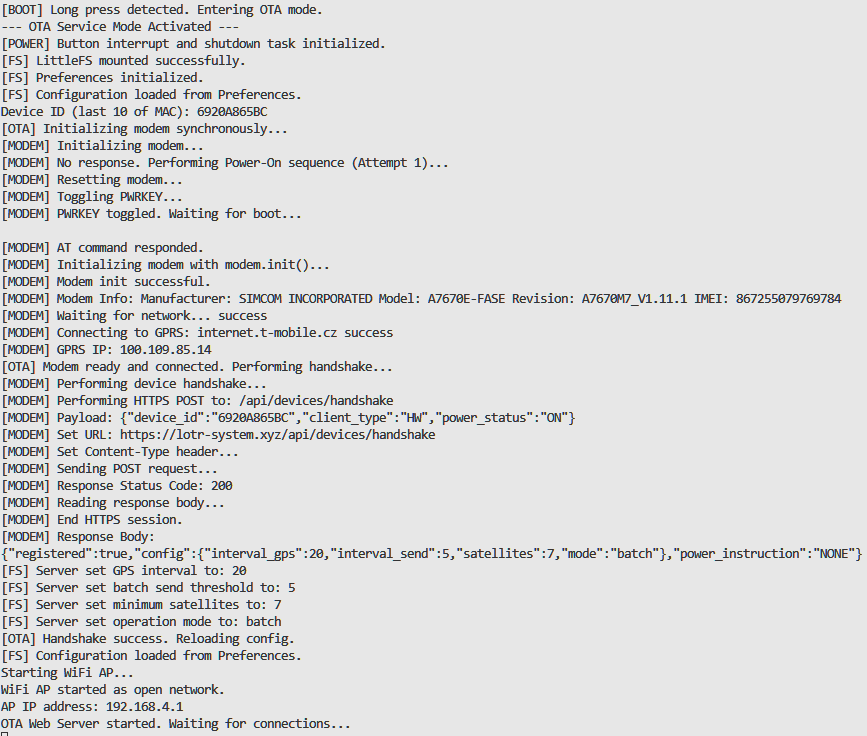
LilyGO-T-A76XX-main/MAIN/FINAL/docs_hw/screenshots/OTA_log_1.png
