Balner123/GPS_server_NodeJS/LilyGO-T-A76XX-main/MAIN/FINAL/docs_hw/screenshots/get_gps_fix.png

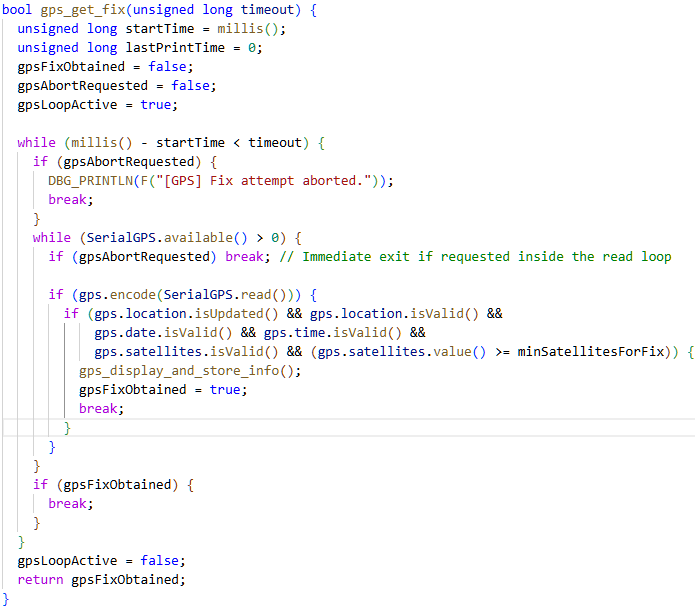
LilyGO-T-A76XX-main/MAIN/FINAL/docs_hw/screenshots/get_gps_fix.png
