Balner123/GPS_server_NodeJS/LilyGO-T-A76XX-main/MAIN/FINAL/file_system.cpp

#include "file_system.h"
#include "ota_mode.h"
#include "modem_control.h"
#include "power_management.h"

#include "freertos/FreeRTOS.h"
#include "freertos/semphr.h"

// Global variables (declared extern in file_system.h and other modules)
String deviceID = "";
String deviceName = DEFAULT_DEVICE_NAME;
String apn = DEFAULT_APN;
String gprsUser = DEFAULT_GPRS_USER;
String gprsPass = DEFAULT_GPRS_PASS;
String server = DEFAULT_SERVER_HOST;
int port = DEFAULT_SERVER_PORT;
uint64_t sleepTimeSeconds = DEFAULT_SLEEP_SECONDS;
bool isRegistered = true; // Assume registered until told otherwise by the server
int minSatellitesForFix = SAT_THRESHOLD;
String operationMode = "batch";
int batchSizeThreshold = DEFAULT_BATCH_SEND_THRESHOLD; // Minimum records in cache to trigger sending

Preferences preferences;

const int MAX_BATCH_SIZE = 15; // Hard limit for the number of records sent in a single POST request
namespace {
SemaphoreHandle_t get_fs_mutex() {
  static portMUX_TYPE initMux = portMUX_INITIALIZER_UNLOCKED;
  static SemaphoreHandle_t fsMutex = nullptr;
  if (fsMutex == nullptr) {
    portENTER_CRITICAL(&initMux);
    if (fsMutex == nullptr) {
      fsMutex = xSemaphoreCreateRecursiveMutex();
    }
    portEXIT_CRITICAL(&initMux);
  }
  return fsMutex;
}

class FsLockGuard {
 public:
  explicit FsLockGuard(TickType_t timeout = portMAX_DELAY) {
    mutex_ = get_fs_mutex();
    locked_ = (mutex_ != nullptr) && (xSemaphoreTakeRecursive(mutex_, timeout) == pdTRUE);
  }

  ~FsLockGuard() {
    if (locked_) {
      xSemaphoreGiveRecursive(mutex_);
    }
  }

  bool isLocked() const { return locked_; }

 private:
  SemaphoreHandle_t mutex_ = nullptr;
  bool locked_ = false;
};
} // namespace

bool fs_init() {
  FsLockGuard lock;
  if (!lock.isLocked()) {
    DBG_PRINTLN(F("[FS] Failed to acquire FS lock during init."));
    return false;
  }
  if (!LittleFS.begin()) {
    DBG_PRINTLN(F("[FS] An Error has occurred while mounting LittleFS"));
    return false;
  }
  DBG_PRINTLN(F("[FS] LittleFS mounted successfully."));
  preferences.begin(PREFERENCES_NAMESPACE, false); // false for read/write
  DBG_PRINTLN(F("[FS] Preferences initialized."));
  return true;
}

void fs_load_configuration() {
  FsLockGuard lock;
  if (!lock.isLocked()) {
    DBG_PRINTLN(F("[FS] Failed to acquire FS lock while loading configuration."));
    return;
  }
  // Load GPRS settings
  if (preferences.isKey("apn")) {
    apn = preferences.getString("apn");
  } else {
    apn = DEFAULT_APN;
  }
  if (preferences.isKey("gprsUser")) {
    gprsUser = preferences.getString("gprsUser");
  } else {
    gprsUser = DEFAULT_GPRS_USER;
  }
  if (preferences.isKey("gprsPass")) {
    gprsPass = preferences.getString("gprsPass");
  } else {
    gprsPass = DEFAULT_GPRS_PASS;
  }

  // Load Server settings
  if (preferences.isKey("server")) {
    server = preferences.getString("server");
  } else {
    server = DEFAULT_SERVER_HOST;
  }
  if (preferences.isKey("port")) {
    port = preferences.getUInt("port");
  } else {
    port = DEFAULT_SERVER_PORT;
  }

  // Load Device settings
  if (preferences.isKey("deviceName")) {
    deviceName = preferences.getString("deviceName");
  } else {
    deviceName = DEFAULT_DEVICE_NAME;
  }
  if (preferences.isKey("mode")) {
    operationMode = preferences.getString("mode");
  } else {
    operationMode = "batch";
  }

  // Load OTA settings
  if (preferences.isKey("ota_ssid")) {
    ota_ssid = preferences.getString("ota_ssid");
  } else {
    ota_ssid = DEFAULT_OTA_SSID;
  }
  // OTA Password removed - always open network
  ota_password = "";

  // Load sleep time, min satellites, and batch send threshold
  if (preferences.isKey("sleepTime")) {
    sleepTimeSeconds = preferences.getULong64("sleepTime");
  } else {
    sleepTimeSeconds = DEFAULT_SLEEP_SECONDS;
  }
  if (preferences.isKey("minSats")) {
    minSatellitesForFix = preferences.getInt("minSats");
  } else {
    minSatellitesForFix = SAT_THRESHOLD;
  }
  if (preferences.isKey(KEY_BATCH_THRESHOLD)) {
    batchSizeThreshold = preferences.getUChar(KEY_BATCH_THRESHOLD);
  } else {
    batchSizeThreshold = DEFAULT_BATCH_SEND_THRESHOLD;
  }
  if (preferences.isKey("registered")) {
    isRegistered = preferences.getBool("registered");
  } else {
    isRegistered = true;
  }

  DBG_PRINTLN(F("[FS] Configuration loaded from Preferences."));
}

void fs_end() {
  FsLockGuard lock;
  if (!lock.isLocked()) {
    DBG_PRINTLN(F("[FS] Failed to acquire FS lock during shutdown."));
    return;
  }
  preferences.end();
  // The mounted() check is not available/needed. LittleFS.end() is safe to call.
  LittleFS.end();
  DBG_PRINTLN(F("[FS] Preferences and LittleFS closed."));
}

void append_to_cache(String jsonRecord) {
  FsLockGuard lock;
  if (!lock.isLocked()) {
    DBG_PRINTLN(F("[FS] Failed to acquire FS lock while appending to cache."));
    return;
  }
  File file = LittleFS.open(CACHE_FILE, "a"); // a = append
  if (!file) {
    DBG_PRINTLN(F("[FS] Failed to open cache file for writing."));
    return;
  }
  if (file.println(jsonRecord)) {
    DBG_PRINTLN(F("[FS] GPS data point appended to cache."));
  } else {
    DBG_PRINTLN(F("[FS] Failed to write to cache file."));
  }
  file.close();
}

bool send_cached_data() {
  FsLockGuard lock;
  if (!lock.isLocked()) {
    DBG_PRINTLN(F("[FS] Failed to acquire FS lock while sending cached data."));
    return false;
  }
  
  bool allDataSent = true;

  while (true) {
    File file = LittleFS.open(CACHE_FILE, "r");
    if (!file || file.size() == 0) {
      if (file) file.close();
      if (allDataSent) {
        DBG_PRINTLN(F("[FS] Cache is empty. All data sent."));
        LittleFS.remove(CACHE_FILE); // Clean up empty file
      }
      return allDataSent;
    }

    String payload = "[";
    bool first = true;
    int recordCount = 0;
    long lastPosition = 0;
    bool batchContainsPowerStatus = false;

    while (file.available() && recordCount < MAX_BATCH_SIZE) {
      String line = file.readStringUntil('\n');
      line.trim();
      if (line.length() > 0) {
        if (!first) {
          payload += ",";
        }
        payload += line;
        first = false;
        recordCount++;
        lastPosition = file.position();
        if (!batchContainsPowerStatus && line.indexOf(F("\"power_status\"")) != -1) {
          batchContainsPowerStatus = true;
        }
      }
    }
    payload += "]";

    if (recordCount == 0) {
      file.close();
      LittleFS.remove(CACHE_FILE); // No valid records found, clear cache
      return true;
    }

    DBG_PRINTF("[FS] Sending batch of %d records...\n", recordCount);
    int httpStatus = 0;
    String response = modem_send_post_request(RESOURCE_POST, payload, &httpStatus);

    if (httpStatus == 404) {
      DBG_PRINTLN(F("[FS] Server returned 404 - device not registered."));
      fs_set_registered(false);
      allDataSent = false;
      file.close();
      break;
    }

    if (httpStatus == 409) {
      DBG_PRINTLN(F("[FS] Server returned 409 - device claimed by another user."));
      fs_set_registered(false);
      allDataSent = false;
      file.close();
      break;
    }

    if (httpStatus >= 500) {
      DBG_PRINT(F("[FS] Server error while sending batch: "));
      DBG_PRINTLN(httpStatus);
      allDataSent = false;
      file.close();
      break;
    }

    JsonDocument serverResponseDoc;
    DeserializationError error = deserializeJson(serverResponseDoc, response);

    if (!error && httpStatus < 400) {
      if (!serverResponseDoc["config"].isNull()) {
        fs_apply_server_config(serverResponseDoc["config"]);
      } else {
        fs_apply_server_config(serverResponseDoc.as<JsonVariantConst>());
      }
      if (!serverResponseDoc["registered"].isNull()) {
        fs_set_registered(serverResponseDoc["registered"].as<bool>());
        if (!isRegistered) {
          DBG_PRINTLN(F("[FS] Server indicated device is not registered."));
        }
      }
    }

    if (!error && serverResponseDoc["success"] == true && httpStatus < 400) {
      DBG_PRINTLN(F("[FS] Batch sent successfully. Updating cache file."));
      if (batchContainsPowerStatus) {
        power_instruction_acknowledged();
        power_status_report_acknowledged();
      }
      
      bool moreData = file.available();
      file.close();

      if (moreData) {
        File tempFile = LittleFS.open("/cache.tmp", "w");
        File originalFile = LittleFS.open(CACHE_FILE, "r");
        if (tempFile && originalFile) {
          originalFile.seek(lastPosition);
          while (originalFile.available()) {
            tempFile.write(originalFile.read());
          }
          tempFile.close();
          originalFile.close();
          LittleFS.remove(CACHE_FILE);
          LittleFS.rename("/cache.tmp", CACHE_FILE);
        } else {
          DBG_PRINTLN(F("[FS] Error creating temp file for cache update."));
          if(tempFile) tempFile.close();
          if(originalFile) originalFile.close();
          allDataSent = false;
          break; 
        }
      } else {
        LittleFS.remove(CACHE_FILE);
        DBG_PRINTLN(F("[FS] All cached data sent."));
        break; 
      }
    } else {
      DBG_PRINTLN(F("[FS] Failed to send batch data. Cache will be kept."));
      if (error) {
        DBG_PRINT(F("[FS] JSON parsing of server response failed: "));
        DBG_PRINTLN(error.c_str());
      }
      if (serverResponseDoc["registered"] == false) {
        DBG_PRINTLN(F("[FS] Server indicated device is not registered. Halting."));
        fs_set_registered(false);
      }
      allDataSent = false;
      file.close();
      break; 
    }
  }
  return allDataSent;
}

bool fs_cache_exists() {
  FsLockGuard lock;
  if (!lock.isLocked()) {
    DBG_PRINTLN(F("[FS] Failed to acquire FS lock while checking cache."));
    return false;
  }
  return LittleFS.exists(CACHE_FILE);
}

void fs_apply_server_config(const JsonVariantConst& config) {
  if (config.isNull()) {
    return;
  }

  FsLockGuard lock;
  if (!lock.isLocked()) {
    DBG_PRINTLN(F("[FS] Failed to acquire FS lock while applying server config."));
    return;
  }

  if (!config["interval_gps"].isNull()) {
    uint64_t interval = config["interval_gps"].as<uint64_t>();
    if (interval > 0) {
      sleepTimeSeconds = interval;
      preferences.putULong64("sleepTime", sleepTimeSeconds);
      DBG_PRINT(F("[FS] Server set GPS interval to: "));
      DBG_PRINTLN(sleepTimeSeconds);
    }
  }

  if (!config["interval_send"].isNull()) {
    uint8_t sendInterval = config["interval_send"].as<uint8_t>();
    if (sendInterval == 0) {
      sendInterval = 1;
    }
    // Ensure batch sending threshold is not greater than the hardcoded MAX_BATCH_SIZE
    if (sendInterval > MAX_BATCH_SIZE) {
      sendInterval = MAX_BATCH_SIZE;
    }
    batchSizeThreshold = sendInterval; // Update global variable
    preferences.putUChar(KEY_BATCH_THRESHOLD, batchSizeThreshold); // Store in preferences
    DBG_PRINT(F("[FS] Server set batch send threshold to: "));
    DBG_PRINTLN(batchSizeThreshold);
  }

  if (!config["satellites"].isNull()) {
    minSatellitesForFix = config["satellites"].as<int>();
    preferences.putInt("minSats", minSatellitesForFix);
    DBG_PRINT(F("[FS] Server set minimum satellites to: "));
    DBG_PRINTLN(minSatellitesForFix);
  }

  if (!config["mode"].isNull()) {
    operationMode = config["mode"].as<String>();
    preferences.putString("mode", operationMode);
    DBG_PRINT(F("[FS] Server set operation mode to: "));
    DBG_PRINTLN(operationMode);
  }
}

void fs_set_registered(bool registered) {
  FsLockGuard lock;
  if (!lock.isLocked()) {
    DBG_PRINTLN(F("[FS] Failed to acquire FS lock while updating registration state."));
    return;
  }
  isRegistered = registered;
  preferences.putBool("registered", registered);
}

size_t fs_get_cache_size() {
  FsLockGuard lock;
  if (!lock.isLocked()) return 0;
  if (!LittleFS.exists(CACHE_FILE)) return 0;
  File file = LittleFS.open(CACHE_FILE, "r");
  size_t size = file.size();
  file.close();
  return size;
}

size_t fs_get_cache_record_count() {
  FsLockGuard lock;
  if (!lock.isLocked()) {
    DBG_PRINTLN(F("[FS] Failed to acquire FS lock while counting cache records."));
    return 0;
  }
  if (!LittleFS.exists(CACHE_FILE)) return 0;

  File file = LittleFS.open(CACHE_FILE, "r");
  if (!file) {
    DBG_PRINTLN(F("[FS] Failed to open cache file for counting records."));
    return 0;
  }

  size_t count = 0;
  while (file.available()) {
    String line = file.readStringUntil('\n');
    line.trim();
    if (line.length() > 0) {
      count++;
    }
  }
  file.close();
  return count;
}

void fs_clear_cache() {
  FsLockGuard lock;
  if (!lock.isLocked()) return;
  if (LittleFS.exists(CACHE_FILE)) {
    LittleFS.remove(CACHE_FILE);
    DBG_PRINTLN(F("[FS] Cache file cleared manually."));
  }
}

void fs_reset_tracking_defaults() {
  {
    FsLockGuard lock;
    if (!lock.isLocked()) {
      DBG_PRINTLN(F("[FS] Failed to acquire FS lock while resetting defaults."));
      return;
    }
    preferences.remove("sleepTime");
    preferences.remove("minSats");
    preferences.remove(KEY_BATCH_THRESHOLD);
    preferences.remove("mode");
    DBG_PRINTLN(F("[FS] Tracking settings keys removed."));
  }
  // Reload to apply defaults to global variables
  fs_load_configuration();
}
